rblack42/math-magik-lpp/rst/design_docs/fuselage/fin/index.rst

assembly: fin
#############

..  include::  design_notes.rst

assembly Design File
********************

..  literalinclude::  ../../../../scad/fuselage/fin/fin.scad
    :linenos:
    :caption: fuselage/fin/fin.scad

Component Data File(s)
**********************

..  literalinclude::  ../../../../scad/fuselage/fin/fin_data.scad
    :linenos:
    :caption: fuselage/fin/fin_data.scad

Components
**********

..  toctree::
    :maxdepth: 1

    rib1/index
    rib2/index
    leading_edge/index
    arc/index
    trailing_edge/index
    covering/index

Component Position File
***********************

..  literalinclude::  ../../../../scad/fuselage/fin/fin_pos.scad
    :linenos:
    :caption: fuselage/fin/fin_pos.scad
