rblack42/math-magik-lpp/rst/design_docs/fuselage/motor_stick/index.rst

part: motor_stick
#################

..  include::  design_notes.rst

part Design File
****************

..  literalinclude::  ../../../../scad/fuselage/motor_stick/motor_stick.scad
    :linenos:
    :caption: fuselage/motor_stick/motor_stick.scad

Component Data File(s)
**********************

..  literalinclude::  ../../../../scad/fuselage/motor_stick/motor_stick_data.scad
    :linenos:
    :caption: fuselage/motor_stick/motor_stick_data.scad
