rblack42/math-magik-lpp/rst/design_docs/fuselage/rear_hook/index.rst

part: rear_hook
###############

..  include::  design_notes.rst

part Design File
****************

..  literalinclude::  ../../../../scad/fuselage/rear_hook/rear_hook.scad
    :linenos:
    :caption: fuselage/rear_hook/rear_hook.scad

Component Data File(s)
**********************

..  literalinclude::  ../../../../scad/fuselage/rear_hook/rear_hook_data.scad
    :linenos:
    :caption: fuselage/rear_hook/rear_hook_data.scad
