rblack42/math-magik-lpp/rst/design_docs/fuselage/stab_post/index.rst

part: stab_post
###############

..  include::  design_notes.rst

part Design File
****************

..  literalinclude::  ../../../../scad/fuselage/stab_post/stab_post.scad
    :linenos:
    :caption: fuselage/stab_post/stab_post.scad

Component Data File(s)
**********************

..  literalinclude::  ../../../../scad/fuselage/stab_post/stab_post_data.scad
    :linenos:
    :caption: fuselage/stab_post/stab_post_data.scad
