rblack42/math-magik-lpp/rst/design_docs/fuselage/tail_boom/index.rst

part: tail_boom
###############

..  include::  design_notes.rst

part Design File
****************

..  literalinclude::  ../../../../scad/fuselage/tail_boom/tail_boom.scad
    :linenos:
    :caption: fuselage/tail_boom/tail_boom.scad

Component Data File(s)
**********************

..  literalinclude::  ../../../../scad/fuselage/tail_boom/tail_boom_data.scad
    :linenos:
    :caption: fuselage/tail_boom/tail_boom_data.scad
