rblack42/math-magik-lpp/rst/design_docs/fuselage/thrust_bearing/index.rst

part: thrust_bearing
####################

..  include::  design_notes.rst

part Design File
****************

..  literalinclude::  ../../../../scad/fuselage/thrust_bearing/thrust_bearing.scad
    :linenos:
    :caption: fuselage/thrust_bearing/thrust_bearing.scad

Component Data File(s)
**********************

..  literalinclude::  ../../../../scad/fuselage/thrust_bearing/thrust_bearing_data.scad
    :linenos:
    :caption: fuselage/thrust_bearing/thrust_bearing_data.scad
