rblack42/math-magik-lpp/rst/design_docs/fuselage/wing_post/index.rst

part: wing_post
###############

..  include::  design_notes.rst

part Design File
****************

..  literalinclude::  ../../../../scad/fuselage/wing_post/wing_post.scad
    :linenos:
    :caption: fuselage/wing_post/wing_post.scad

Component Data File(s)
**********************

..  literalinclude::  ../../../../scad/fuselage/wing_post/wing_post_data.scad
    :linenos:
    :caption: fuselage/wing_post/wing_post_data.scad
