rblack42/math-magik-lpp/rst/design_docs/prop/blade/index.rst

part: blade
###########

..  include::  design_notes.rst

part Design File
****************

..  literalinclude::  ../../../../scad/prop/blade/blade.scad
    :linenos:
    :caption: prop/blade/blade.scad
