rblack42/math-magik-lpp/rst/design_docs/prop/spar/index.rst

part: spar
##########

..  include::  design_notes.rst

part Design File
****************

..  literalinclude::  ../../../../scad/prop/spar/spar.scad
    :linenos:
    :caption: prop/spar/spar.scad
