rblack42/math-magik-lpp/rst/design_docs/prop/wire_shaft/index.rst

part: wire_shaft
################

..  include::  design_notes.rst

part Design File
****************

..  literalinclude::  ../../../../scad/prop/wire_shaft/wire_shaft.scad
    :linenos:
    :caption: prop/wire_shaft/wire_shaft.scad
