rblack42/math-magik-lpp/rst/design_docs/stab/left_tip/index.rst

assembly: left_tip
##################

..  include::  design_notes.rst

assembly Design File
********************

..  literalinclude::  ../../../../scad/stab/left_tip/left_tip.scad
    :linenos:
    :caption: stab/left_tip/left_tip.scad

Components
**********

..  toctree::
    :maxdepth: 1

    tip_rib/index
    tip_arc/index
    leading_edge/index
    trailing_edge/index
    covering/index

Component Position File
***********************

..  literalinclude::  ../../../../scad/stab/left_tip/left_tip_pos.scad
    :linenos:
    :caption: stab/left_tip/left_tip_pos.scad
