rblack42/math-magik-lpp/rst/design_docs/wing/center/index.rst

assembly: center
################

..  include::  design_notes.rst

assembly Design File
********************

..  literalinclude::  ../../../../scad/wing/center/center.scad
    :linenos:
    :caption: wing/center/center.scad

Components
**********

..  toctree::
    :maxdepth: 1

    rib/index
    spar/index
    covering/index

Component Position File
***********************

..  literalinclude::  ../../../../scad/wing/center/center_pos.scad
    :linenos:
    :caption: wing/center/center_pos.scad
