rblack42/math-magik-lpp/rst/design_docs/wing/right_tip/index.rst

part: right_tip
###############

..  include::  design_notes.rst

part Design File
****************

..  literalinclude::  ../../../../scad/wing/right_tip/right_tip.scad
    :linenos:
    :caption: wing/right_tip/right_tip.scad
