rblack42/math-magik-lpp/rst/design_docs/wing/Wing_mount/index.rst

part: wing_mount
################

..  include::  design_notes.rst

part Design File
****************

..  literalinclude::  ../../../../scad/wing/Wing_mount/wing_mount.scad
    :linenos:
    :caption: wing/Wing_mount/wing_mount.scad
