rblack42/math-magik-lpp/mmdesigner/fuselage/fin_postrst/design_docs/index.rst

part: 
######

This part is created with the following file:

..  literalinclude::  ../../../scad/fuselage/fin_post/.scad
    :linenos:
    :caption: fuselage/fin_post/.scad
