rblack42/math-magik-lpp/mmdesigner/fuselage/stab_postrst/design_docs/index.rst

part: 
######

This part is created with the following file:

..  literalinclude::  ../../../scad/fuselage/stab_post/.scad
    :linenos:
    :caption: fuselage/stab_post/.scad

Component Data File(s)
**********************

..  literalinclude::  ../scad/fuselage/stab_post/stab_post_data.scad
