rblack42/math-magik-lpp/mmdesigner/fuselage/wing_postrst/design_docs/index.rst

part: 
######

This part is created with the following file:

..  literalinclude::  ../../../scad/fuselage/wing_post/.scad
    :linenos:
    :caption: fuselage/wing_post/.scad

Component Data File(s)
**********************

..  literalinclude::  ../scad/fuselage/wing_post/wing_post_data.scad
