rblack42/math-magik-lpp/mmdesigner/prop/bladerst/design_docs/index.rst

part: blade
###########

This part is created with the following file:

..  literalinclude::  ../../../scad/prop/blade/blade.scad
    :linenos:
    :caption: prop/blade/blade.scad
