rblack42/math-magik-lpp/mmdesigner/prop/sparrst/design_docs/index.rst

part: spar
##########

This part is created with the following file:

..  literalinclude::  ../../../scad/prop/spar/spar.scad
    :linenos:
    :caption: prop/spar/spar.scad
