rblack42/math-magik-lpp/mmdesigner/prop/wire_shaftrst/design_docs/index.rst

part: wire_shaft
################

This part is created with the following file:

..  literalinclude::  ../../../scad/prop/wire_shaft/wire_shaft.scad
    :linenos:
    :caption: prop/wire_shaft/wire_shaft.scad
