rblack42/math-magik-lpp/mmdesigner/wing/right_tiprst/design_docs/index.rst

part: right_tip
###############

This part is created with the following file:

..  literalinclude::  ../../../scad/wing/right_tip/right_tip.scad
    :linenos:
    :caption: wing/right_tip/right_tip.scad
