rblack42/math-magik-lpp/mmdesigner/wing/Wing_mountrst/design_docs/index.rst

part: wing_mount
################

This part is created with the following file:

..  literalinclude::  ../../../scad/wing/Wing_mount/wing_mount.scad
    :linenos:
    :caption: wing/Wing_mount/wing_mount.scad
