rblack42/math-magik-lpp/rst/design_docs/fuselage/fin/arc/index.rst

part: fin_arc
#############

..  include::  design_notes.rst

part Design File
****************

..  literalinclude::  ../../../../../scad/fuselage/fin/arc/fin_arc.scad
    :linenos:
    :caption: fuselage/fin/arc/fin_arc.scad
