rblack42/math-magik-lpp/rst/design_docs/fuselage/fin/covering/index.rst

part: fin_covering
##################

..  include::  design_notes.rst

part Design File
****************

..  literalinclude::  ../../../../../scad/fuselage/fin/covering/fin_covering.scad
    :linenos:
    :caption: fuselage/fin/covering/fin_covering.scad

Component Data File(s)
**********************

..  literalinclude::  ../../../../../scad/fuselage/fin/covering/cover_points.scad
    :linenos:
    :caption: fuselage/fin/covering/cover_points.scad
