rblack42/math-magik-lpp/rst/design_docs/fuselage/fin/leading_edge/index.rst

part: leading_edge
##################

..  include::  design_notes.rst

part Design File
****************

..  literalinclude::  ../../../../../scad/fuselage/fin/leading_edge/leading_edge.scad
    :linenos:
    :caption: fuselage/fin/leading_edge/leading_edge.scad
