rblack42/math-magik-lpp/rst/design_docs/fuselage/fin/rib1/index.rst

part: fin_rib1
##############

..  include::  design_notes.rst

part Design File
****************

..  literalinclude::  ../../../../../scad/fuselage/fin/rib1/fin_rib1.scad
    :linenos:
    :caption: fuselage/fin/rib1/fin_rib1.scad
