rblack42/math-magik-lpp/rst/design_docs/fuselage/fin/rib2/index.rst

part: fin_rib2
##############

..  include::  design_notes.rst

part Design File
****************

..  literalinclude::  ../../../../../scad/fuselage/fin/rib2/fin_rib2.scad
    :linenos:
    :caption: fuselage/fin/rib2/fin_rib2.scad
