rblack42/math-magik-lpp/rst/design_docs/fuselage/fin/trailing_edge/index.rst

part: trailing_edge
###################

..  include::  design_notes.rst

part Design File
****************

..  literalinclude::  ../../../../../scad/fuselage/fin/trailing_edge/trailing_edge.scad
    :linenos:
    :caption: fuselage/fin/trailing_edge/trailing_edge.scad
