rblack42/math-magik-lpp/rst/design_docs/wing/center/covering/index.rst

part: covering
##############

..  include::  design_notes.rst

part Design File
****************

..  literalinclude::  ../../../../../scad/wing/center/covering/covering.scad
    :linenos:
    :caption: wing/center/covering/covering.scad

Component Data File(s)
**********************

..  literalinclude::  ../../../../../scad/wing/center/covering/cover_points.scad
    :linenos:
    :caption: wing/center/covering/cover_points.scad
