rblack42/math-magik-lpp/rst/design_docs/wing/center/rib/index.rst

part: rib
#########

..  include::  design_notes.rst

part Design File
****************

..  literalinclude::  ../../../../../scad/wing/center/rib/rib.scad
    :linenos:
    :caption: wing/center/rib/rib.scad
