rblack42/math-magik-lpp/rst/design_docs/wing/center/spar/index.rst

part: spar
##########

..  include::  design_notes.rst

part Design File
****************

..  literalinclude::  ../../../../../scad/wing/center/spar/spar.scad
    :linenos:
    :caption: wing/center/spar/spar.scad
