rblack42/math-magik-lpp/rst/design_docs/wing/left_tip/covering/index.rst

part: covering
##############

..  include::  design_notes.rst

part Design File
****************

..  literalinclude::  ../../../../../scad/wing/left_tip/covering/covering.scad
    :linenos:
    :caption: wing/left_tip/covering/covering.scad

Component Data File(s)
**********************

..  literalinclude::  ../../../../../scad/wing/left_tip/covering/cover_points.scad
    :linenos:
    :caption: wing/left_tip/covering/cover_points.scad
