rblack42/math-magik-lpp/rst/design_docs/wing/left_tip/leading_edge/index.rst

part: leading_edge
##################

..  include::  design_notes.rst

part Design File
****************

..  literalinclude::  ../../../../../scad/wing/left_tip/leading_edge/leading_edge.scad
    :linenos:
    :caption: wing/left_tip/leading_edge/leading_edge.scad
