rblack42/math-magik-lpp/rst/design_docs/wing/left_tip/tip_arc/index.rst

part: tip_arc
#############

..  include::  design_notes.rst

part Design File
****************

..  literalinclude::  ../../../../../scad/wing/left_tip/tip_arc/tip_arc.scad
    :linenos:
    :caption: wing/left_tip/tip_arc/tip_arc.scad
