rblack42/math-magik-lpp/rst/design_docs/wing/left_tip/tip_rib/index.rst

part: tip_rib
#############

..  include::  design_notes.rst

part Design File
****************

..  literalinclude::  ../../../../../scad/wing/left_tip/tip_rib/tip_rib.scad
    :linenos:
    :caption: wing/left_tip/tip_rib/tip_rib.scad
