rblack42/math-magik-lpp/rst/design_docs/wing/left_tip/trailing_edge/index.rst

part: trailing_edge
###################

..  include::  design_notes.rst

part Design File
****************

..  literalinclude::  ../../../../../scad/wing/left_tip/trailing_edge/trailing_edge.scad
    :linenos:
    :caption: wing/left_tip/trailing_edge/trailing_edge.scad
