rblack42/math-magik-lpp/rst/spelling_wordlist.txt

appveyor
Bigge
bumpversion
cd
cfg
ci
cli
cmd
dev
devnotes
Fairfax
forwardmost
gh
github
gz
Hodson
HTML
init
kbd
Lakehurst
lpp
Macbook
Magik
magik
makefile
Makefile
Makefiles
mmdesigner
nojekyll
numpy
openscad
ornithopter
Pennyplane
py
pypi
rblack
rearmost
readme
repo
rst
slusarczyk
stl
subdirectory
subdirectories
subfolder

Todo
travis
txt
ubuntu
whl
yml
