rblack42/math-magik-lpp/docs/_images/blade.png

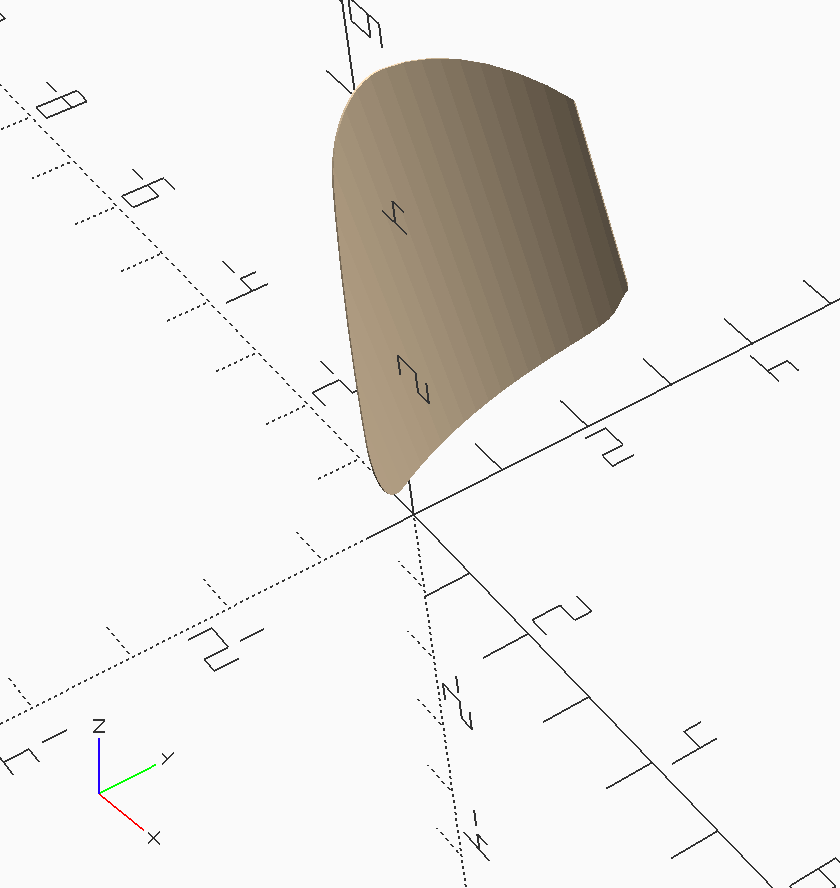
docs/_images/blade.png
