rblack42/math-magik-lpp/docs/_images/double_taper_spar.png

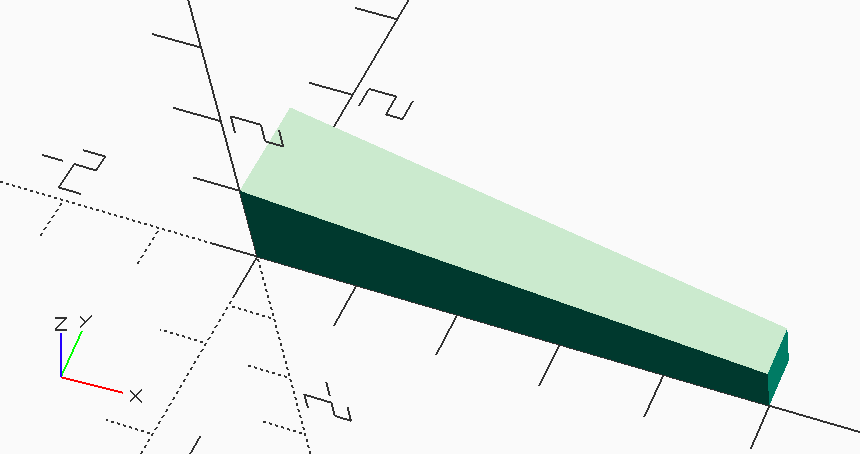
docs/_images/double_taper_spar.png
