rblack42/math-magik-lpp/docs/_images/fuselage.png

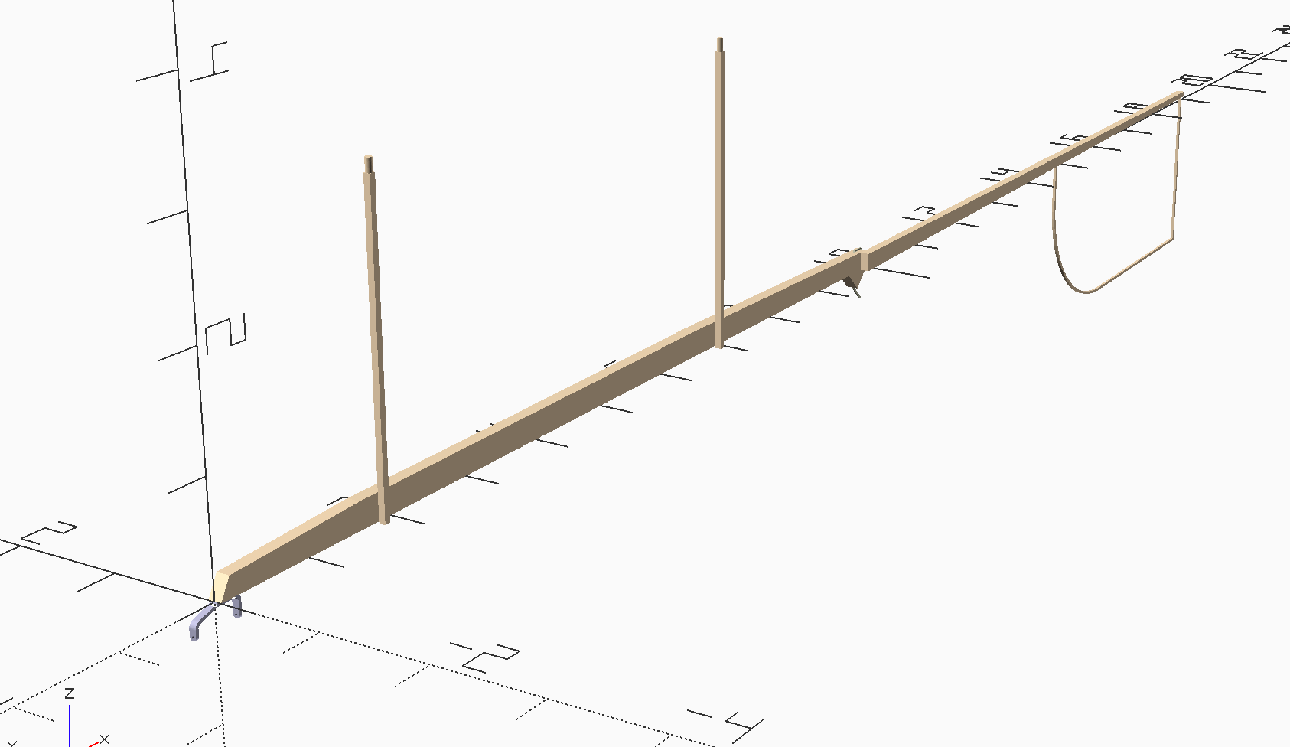
docs/_images/fuselage.png
