rblack42/math-magik-lpp/docs/_images/left_tip.png

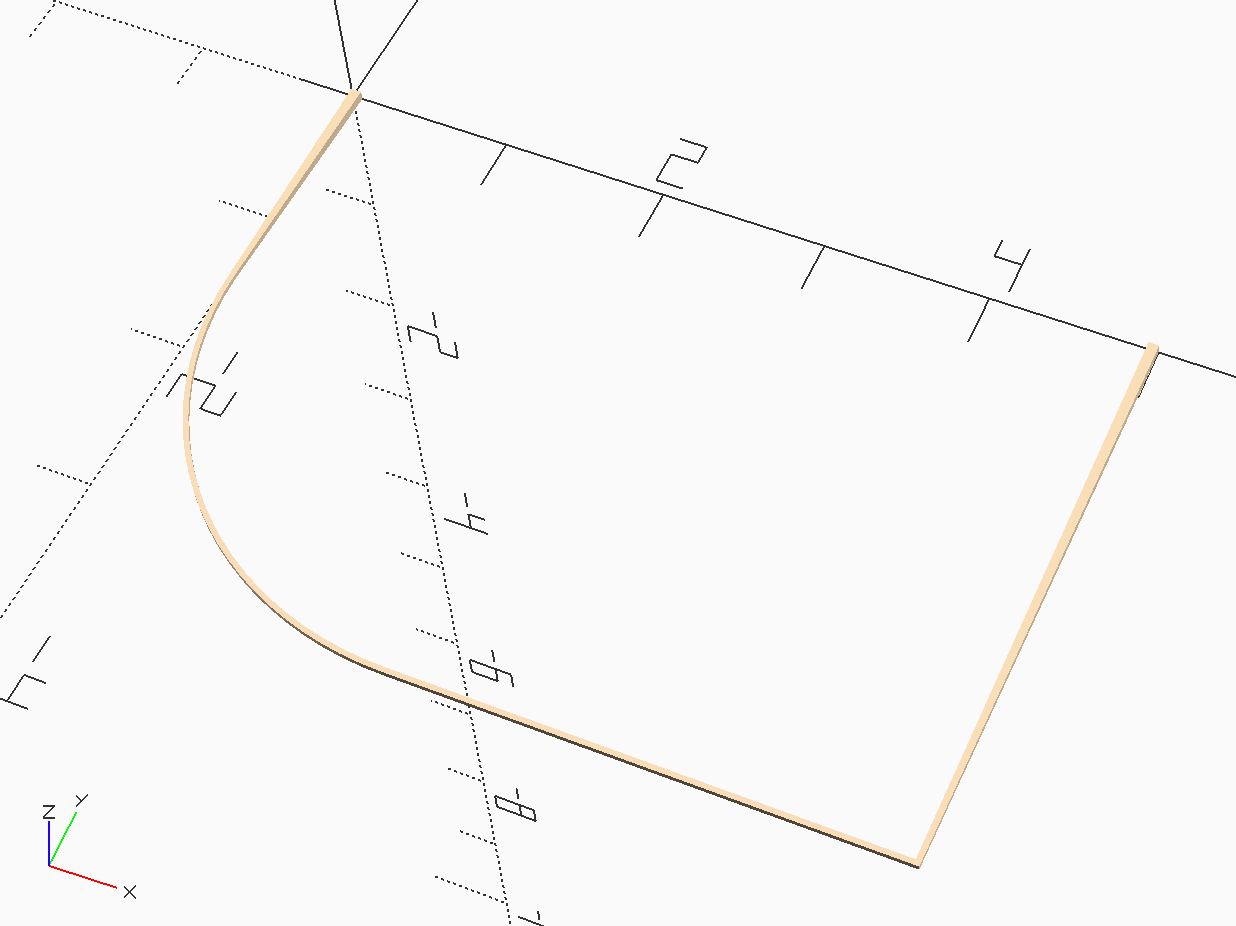
docs/_images/left_tip.png
