rblack42/math-magik-lpp/docs/_images/motor_stick.png

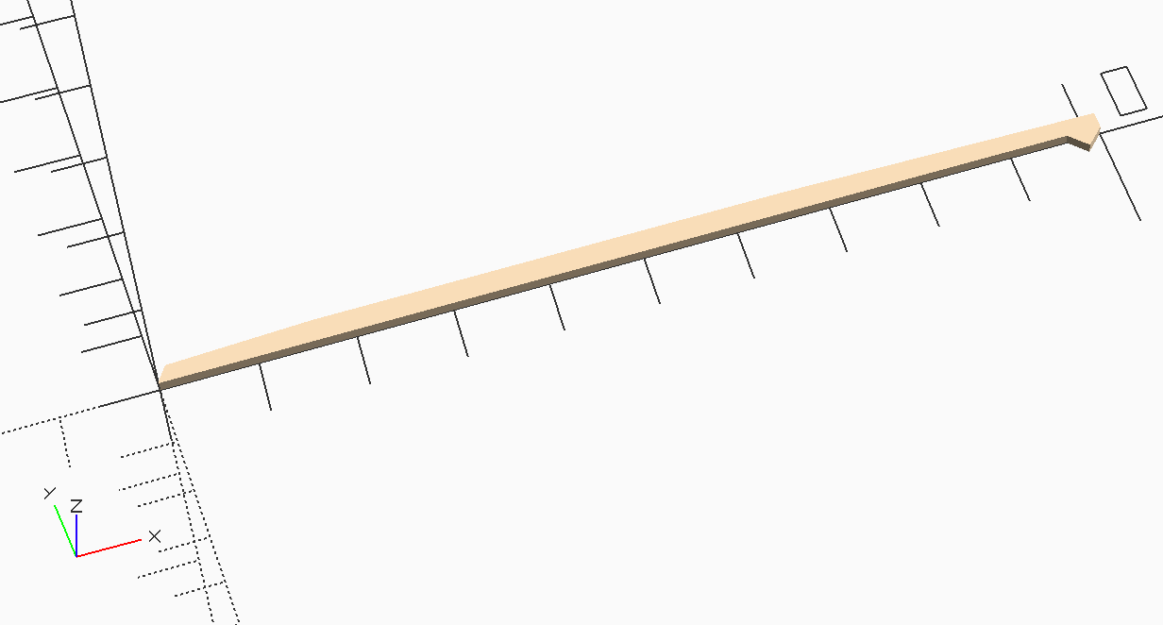
docs/_images/motor_stick.png
