rblack42/math-magik-lpp/docs/_images/prop.png

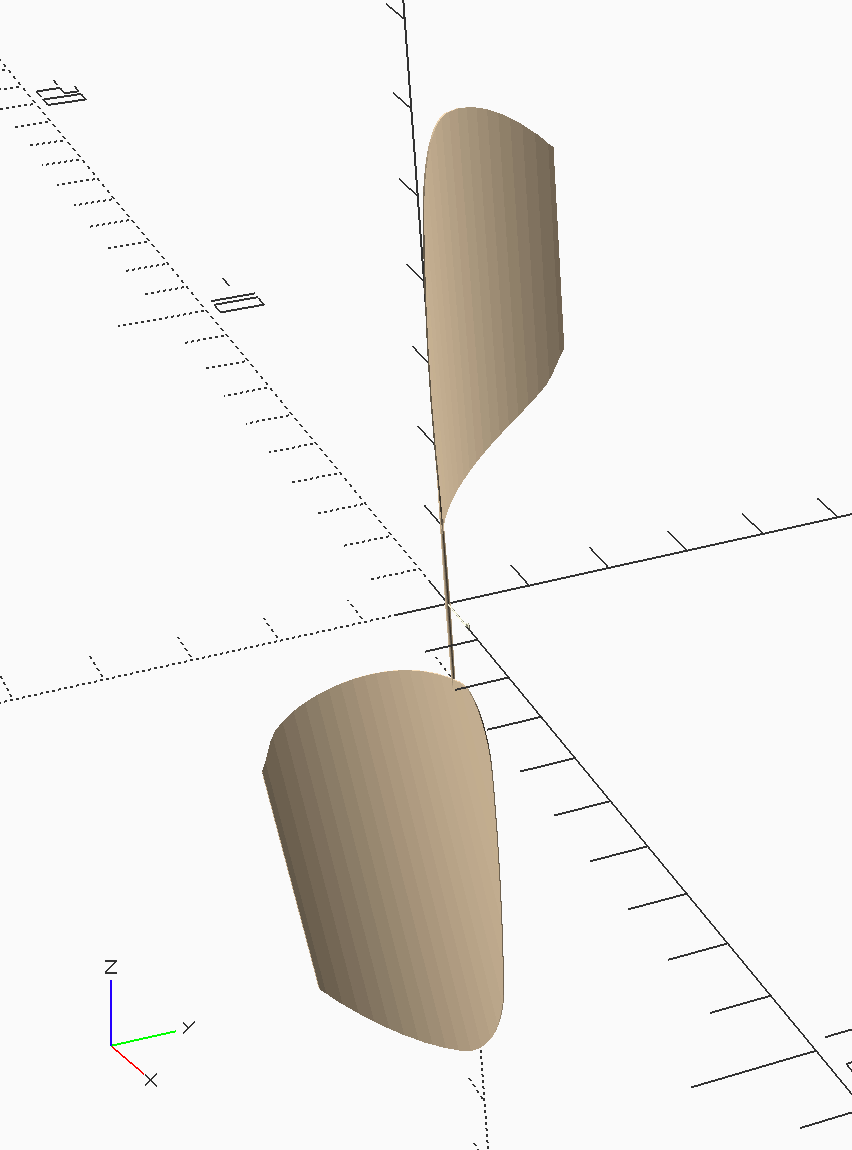
docs/_images/prop.png
