rblack42/math-magik-lpp/docs/_images/rear_hook.png

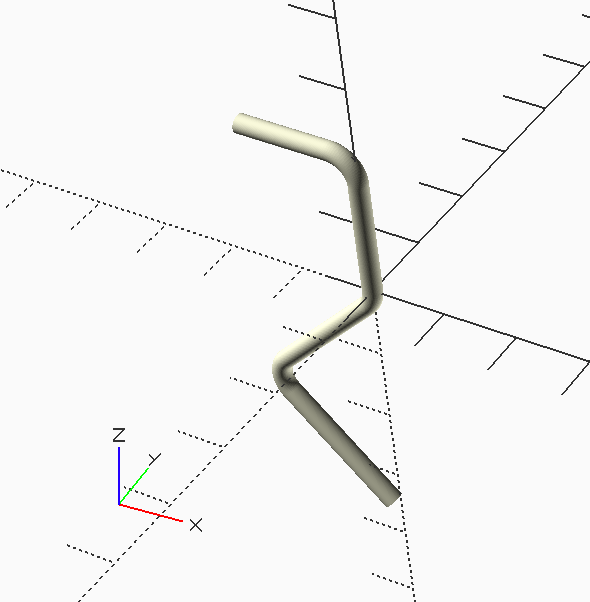
docs/_images/rear_hook.png
