rblack42/math-magik-lpp/docs/_images/rib.png

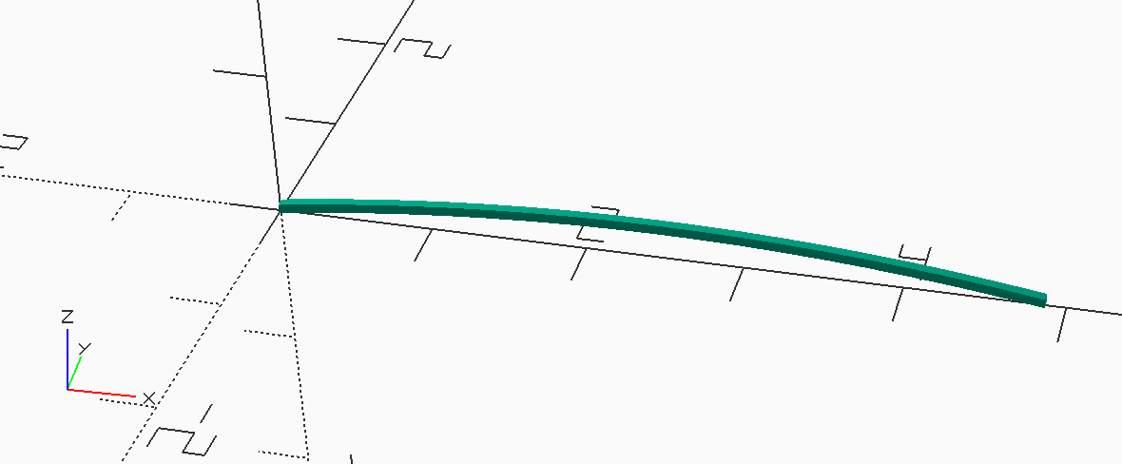
docs/_images/rib.png
