rblack42/math-magik-lpp/docs/_images/rounded_post.png

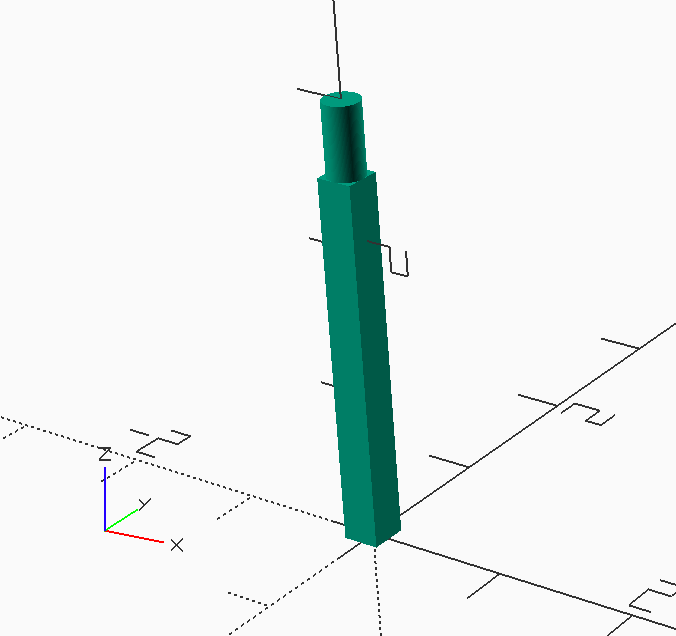
docs/_images/rounded_post.png
