rblack42/math-magik-lpp/docs/_images/single_taper_spar.png

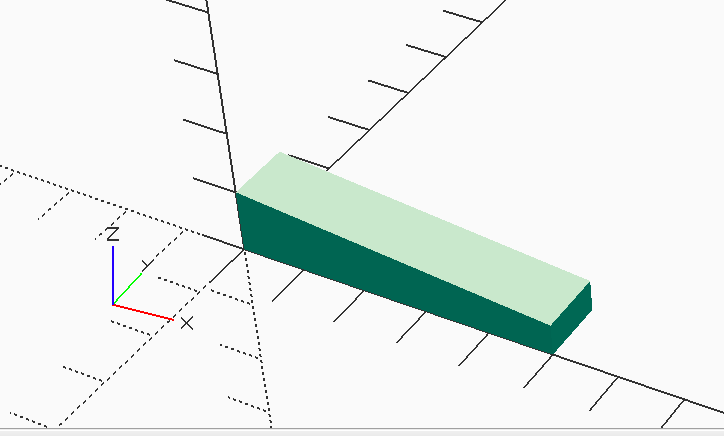
docs/_images/single_taper_spar.png
