rblack42/math-magik-lpp/docs/_images/square_spar.png

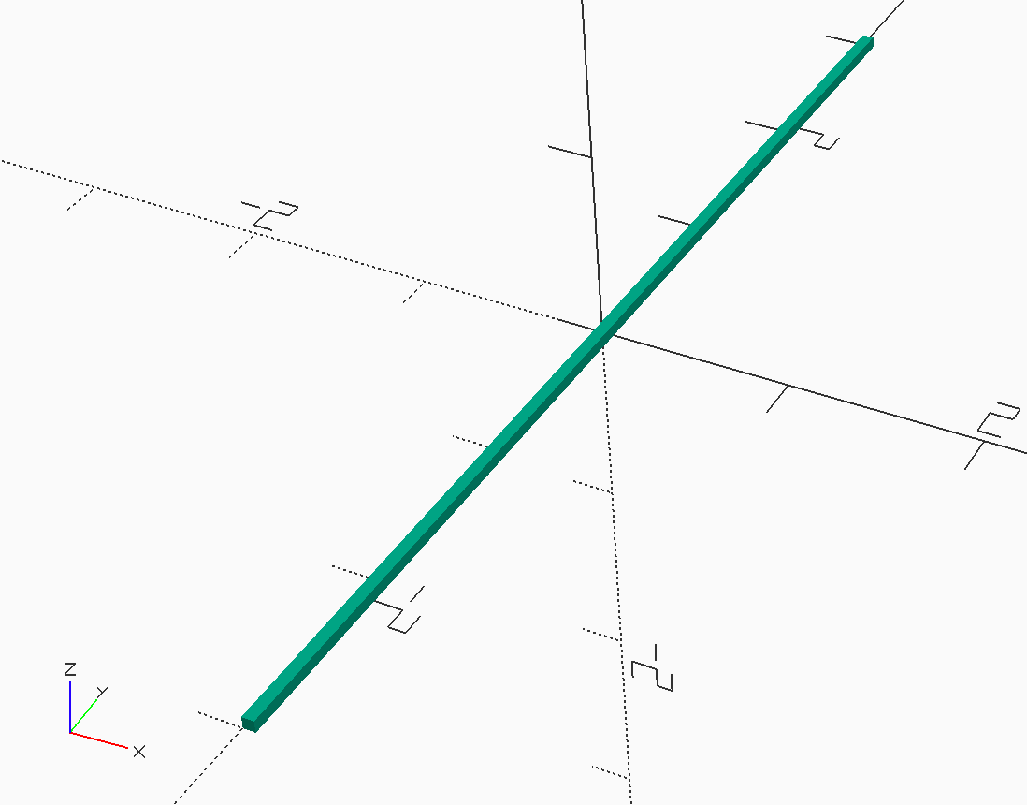
docs/_images/square_spar.png
