rblack42/math-magik-lpp/docs/_images/stab_center.png

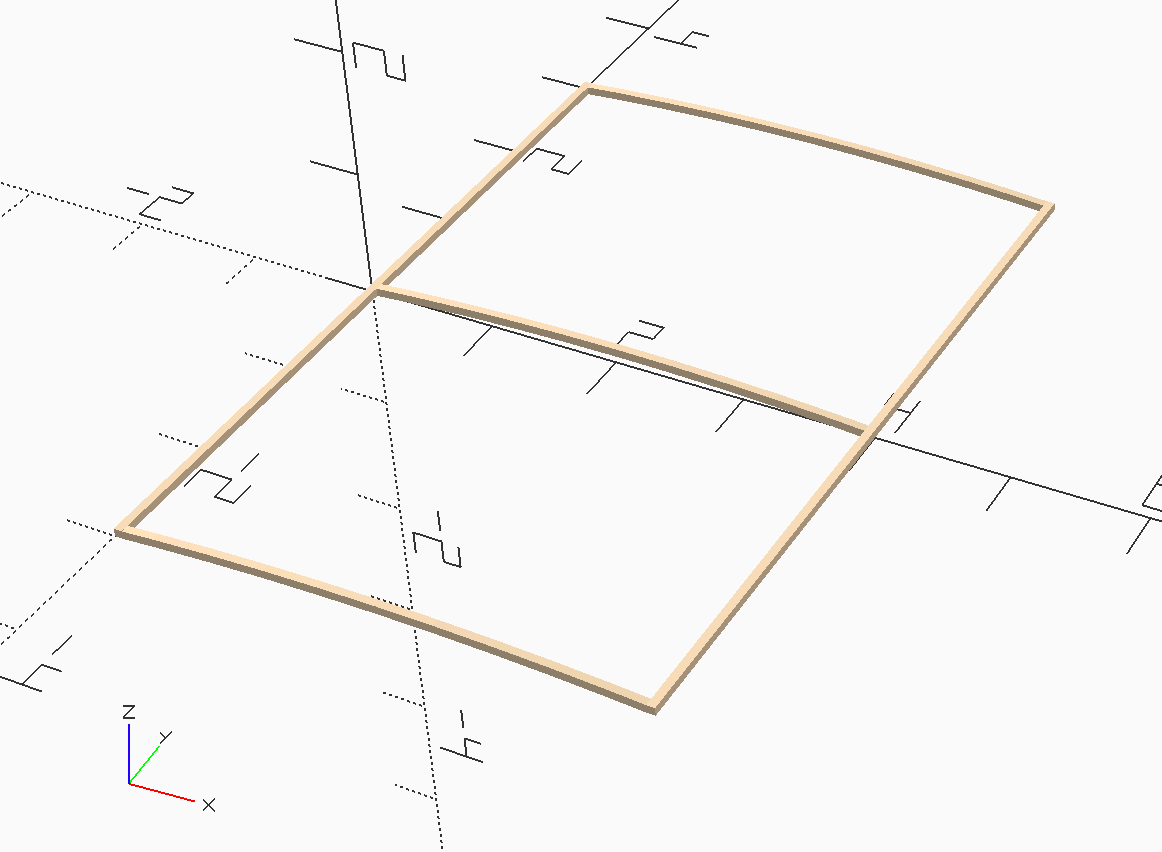
docs/_images/stab_center.png
