rblack42/math-magik-lpp/docs/_images/thrust_bearing.png

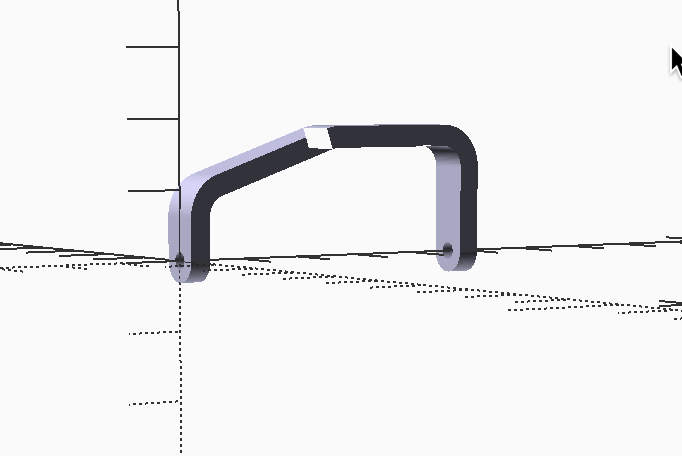
docs/_images/thrust_bearing.png
