rblack42/math-magik-lpp/docs/_images/tikz-1e1b6ad982377da549f57b0fc93ea1e75415a15b.png

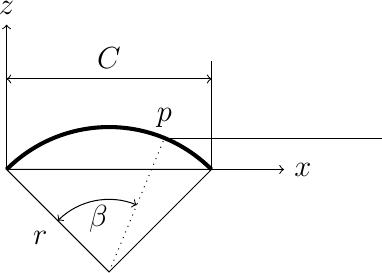
docs/_images/tikz-1e1b6ad982377da549f57b0fc93ea1e75415a15b.png
