rblack42/math-magik-lpp/docs/_images/tikz-3c3cd3720b0a94dc857fa89500e327e3fa3e4184.png

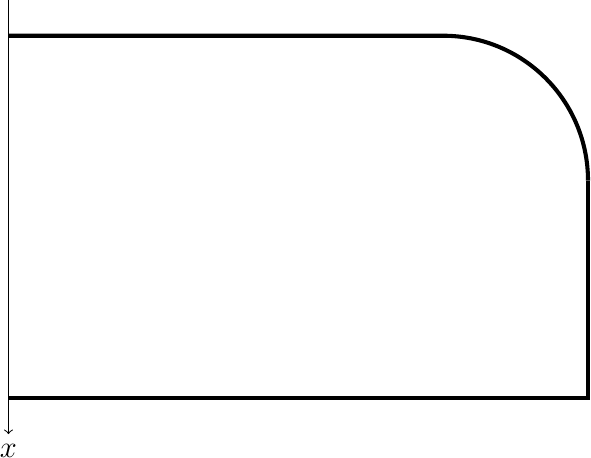
docs/_images/tikz-3c3cd3720b0a94dc857fa89500e327e3fa3e4184.png
