rblack42/math-magik-lpp/docs/_images/tikz-4f54b4c82ac9a10f0b2b195eb7bd98474e7d9e88.png

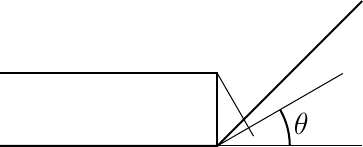
docs/_images/tikz-4f54b4c82ac9a10f0b2b195eb7bd98474e7d9e88.png
