rblack42/math-magik-lpp/docs/_images/tikz-6e44ed49dc1ec410e66353efb7aa8f4e9786132d.png

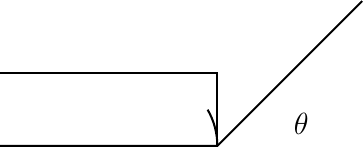
docs/_images/tikz-6e44ed49dc1ec410e66353efb7aa8f4e9786132d.png
