rblack42/math-magik-lpp/docs/_images/tikz-15ca8c3aa0b2c31cfb2b1e34143b804b3e2dcef0.png

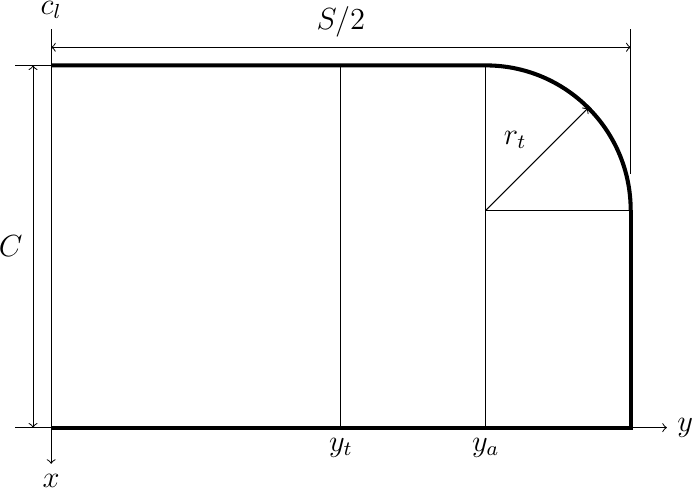
docs/_images/tikz-15ca8c3aa0b2c31cfb2b1e34143b804b3e2dcef0.png
