rblack42/math-magik-lpp/docs/_images/tikz-27d1260bff673aa3068d1d6eca676e5026bad99a.png

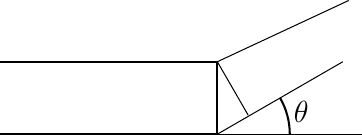
docs/_images/tikz-27d1260bff673aa3068d1d6eca676e5026bad99a.png
