rblack42/math-magik-lpp/docs/_images/tikz-44dbda32ecce6ddc4b5006c9e633f6ff90a8a992.png

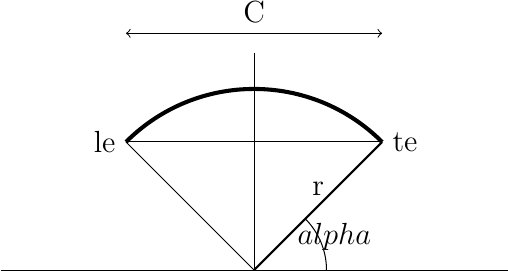
docs/_images/tikz-44dbda32ecce6ddc4b5006c9e633f6ff90a8a992.png
