rblack42/math-magik-lpp/docs/_images/tikz-316b7be6a84d6f8fb4f3c9a147262586597630df.png

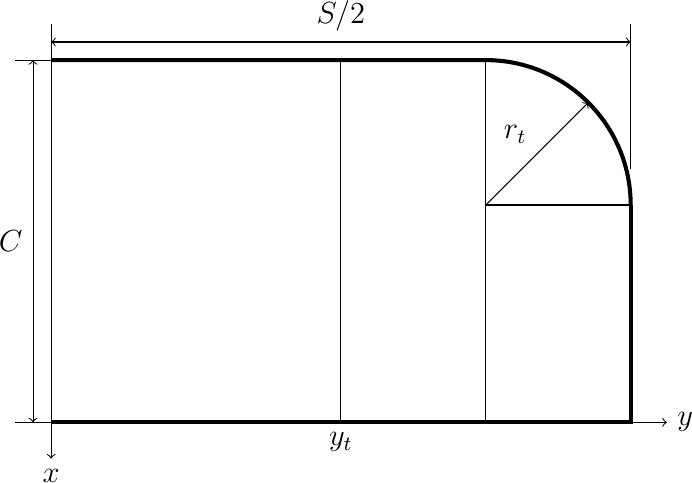
docs/_images/tikz-316b7be6a84d6f8fb4f3c9a147262586597630df.png
