rblack42/math-magik-lpp/docs/_images/tikz-8070c85ff5d8f88f2f3264d625a20d863a9753f6.png

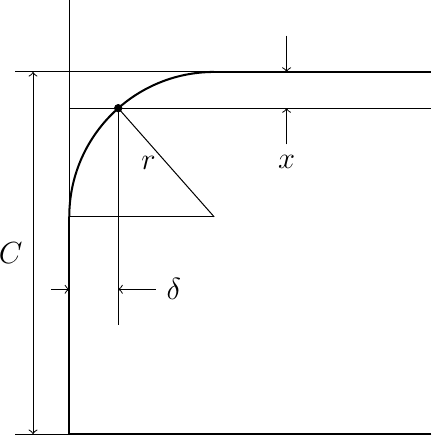
docs/_images/tikz-8070c85ff5d8f88f2f3264d625a20d863a9753f6.png
