rblack42/math-magik-lpp/docs/_images/tikz-32207ebea0998a1cce49b7c706ef4b8a1087978a.png

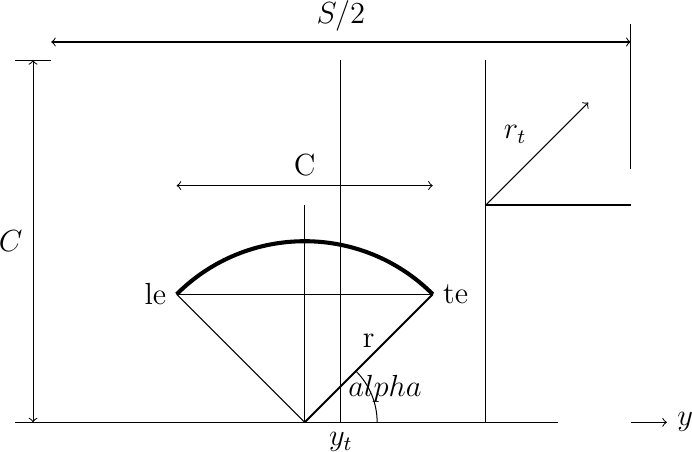
docs/_images/tikz-32207ebea0998a1cce49b7c706ef4b8a1087978a.png
