rblack42/math-magik-lpp/docs/_images/tip_arc.png

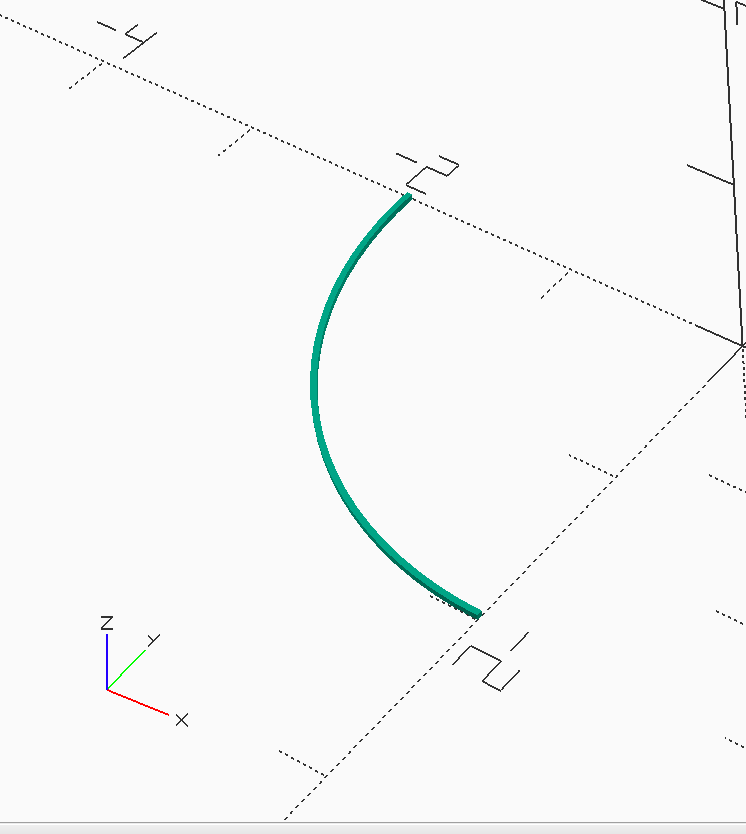
docs/_images/tip_arc.png
