rblack42/math-magik-lpp/docs/_images/wire_shaft.png

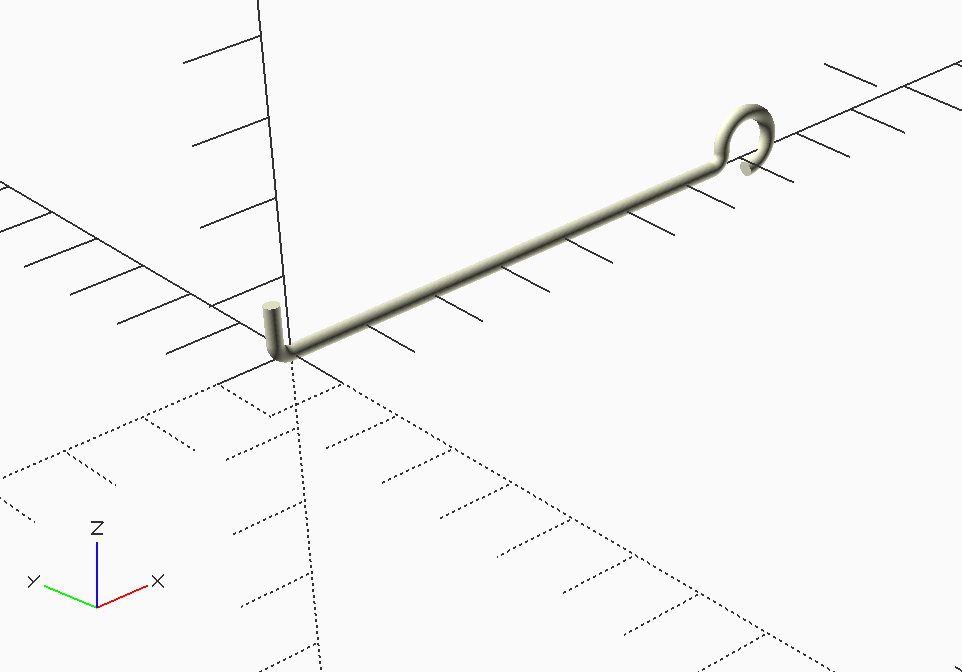
docs/_images/wire_shaft.png
