rblack42/math-magik-lpp/rst/images/mac-terminal.png

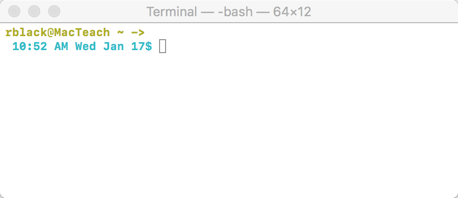
rst/images/mac-terminal.png
