rblack42/math-magik-lpp/scad/math-magik-lpp/prop/spar/spar.stl

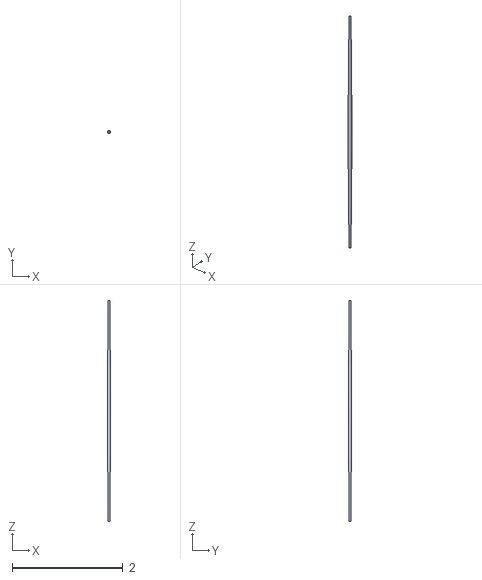
[picture p47: CAD file, 2021-09-04]
scad/math-magik-lpp/prop/spar/spar.stl
0.0625 x 0.0625 x 4.00
