rblack42/math-magik-lpp/scad/math-magik-lpp/rubber_motor/rubber_motor.stl

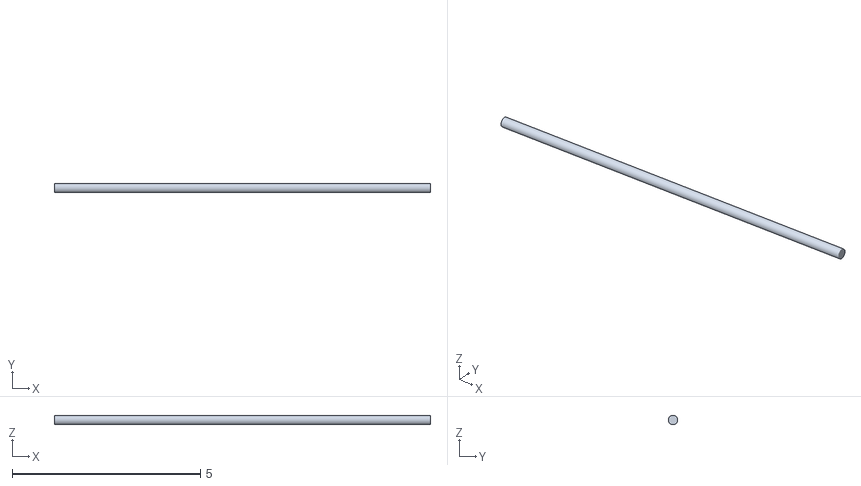
[picture p48: CAD file, 2021-09-04]
scad/math-magik-lpp/rubber_motor/rubber_motor.stl
10.0 x 0.25 x 0.25
