rblack42/math-magik-lpp/scad/math-magik-lpp/stab/center/covering/covering.stl

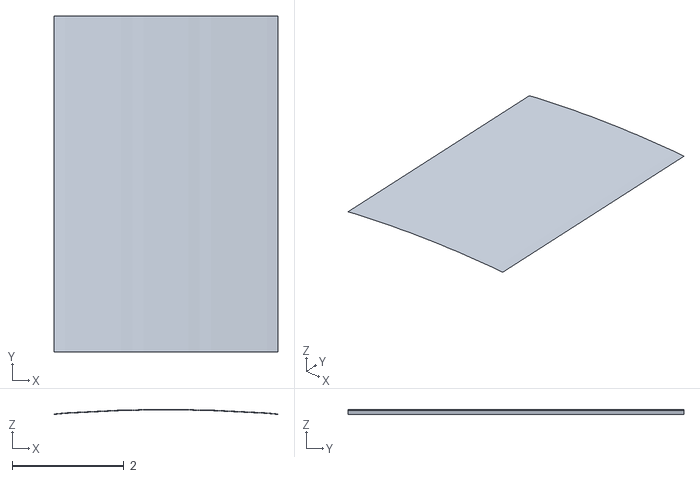
[picture p49: CAD file, 2021-09-04]
scad/math-magik-lpp/stab/center/covering/covering.stl
4.00 x 6.00 x 0.081
