rblack42/math-magik-lpp/scad/math-magik-lpp/stab/center/rib/rib.stl

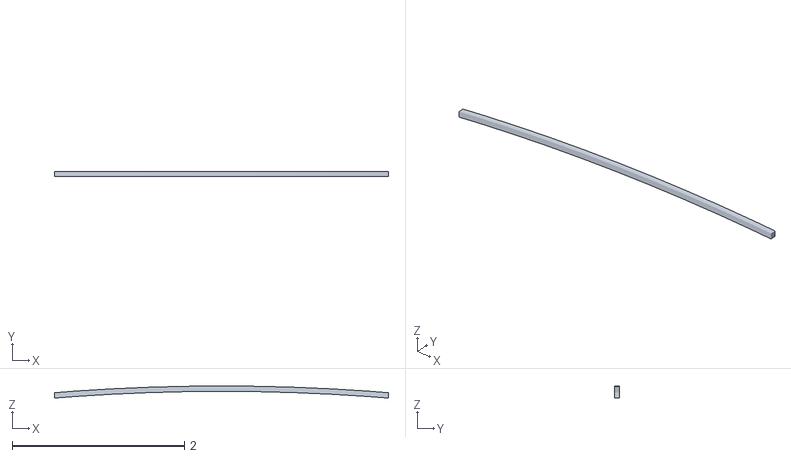
[picture p50: CAD file, 2021-09-04]
scad/math-magik-lpp/stab/center/rib/rib.stl
3.88 x 0.0625 x 0.14
