rblack42/math-magik-lpp/scad/math-magik-lpp/stab/center/spar/spar.stl

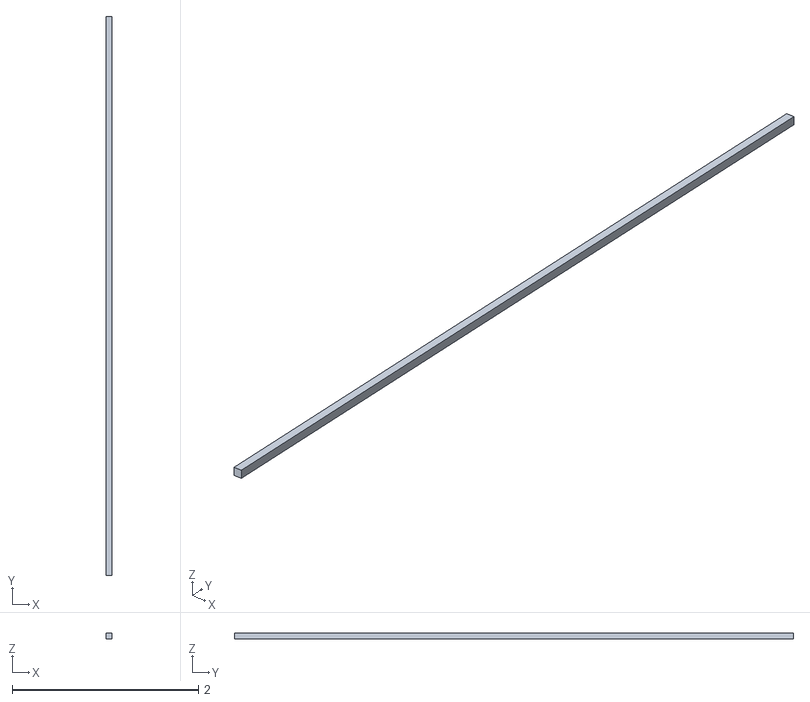
[picture p51: CAD file, 2021-09-04]
scad/math-magik-lpp/stab/center/spar/spar.stl
0.0625 x 6.00 x 0.0625
