rblack42/math-magik-lpp/scad/math-magik-lpp/stab/left_tip/covering/covering.stl

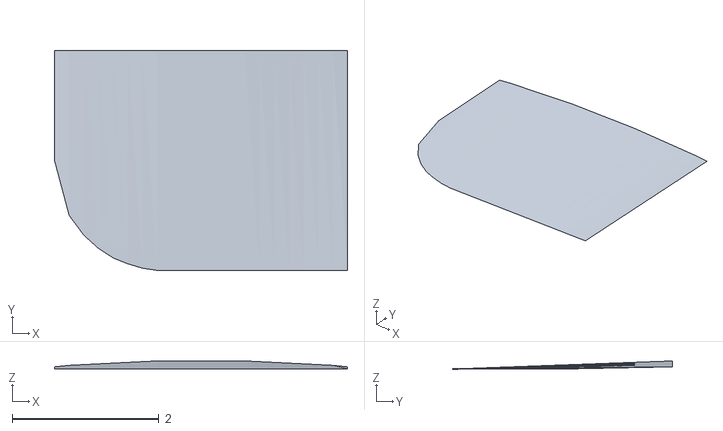
[picture p52: CAD file, 2021-09-04]
scad/math-magik-lpp/stab/left_tip/covering/covering.stl
4.00 x 3.00 x 0.111
