rblack42/math-magik-lpp/scad/math-magik-lpp/stab/left_tip/leading_edge/leading_edge.stl

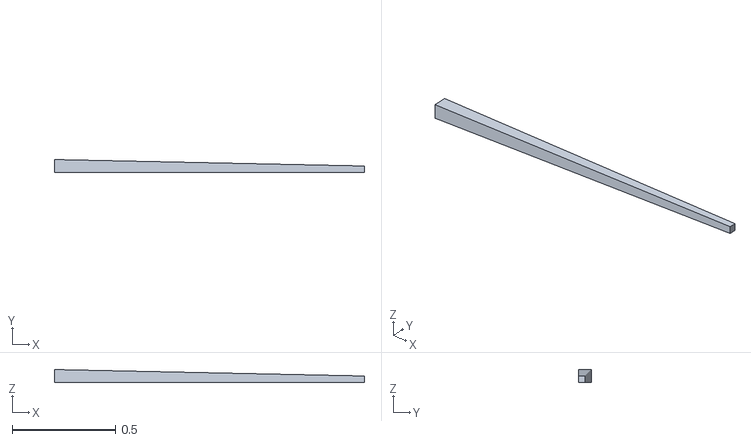
[picture p53: CAD file, 2021-09-04]
scad/math-magik-lpp/stab/left_tip/leading_edge/leading_edge.stl
1.50 x 0.0625 x 0.0625
