rblack42/math-magik-lpp/scad/math-magik-lpp/stab/left_tip/tip_rib/tip_rib.stl

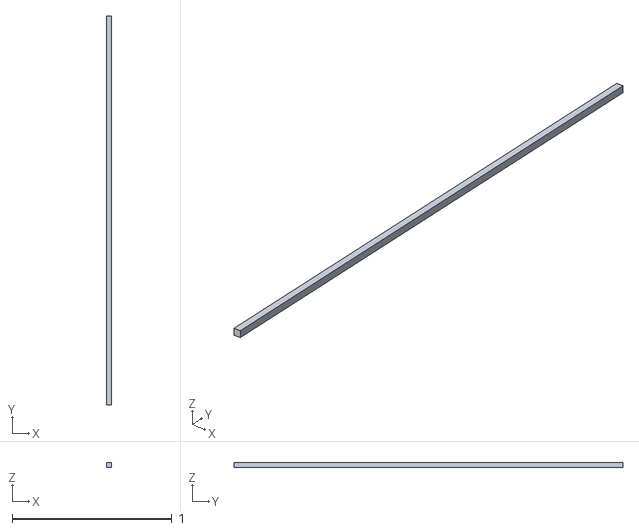
[picture p54: CAD file, 2021-09-04]
scad/math-magik-lpp/stab/left_tip/tip_rib/tip_rib.stl
0.0312 x 2.44 x 0.0312
