rblack42/math-magik-lpp/scad/math-magik-lpp/stab/left_tip/trailing_edge/trailing_edge.stl

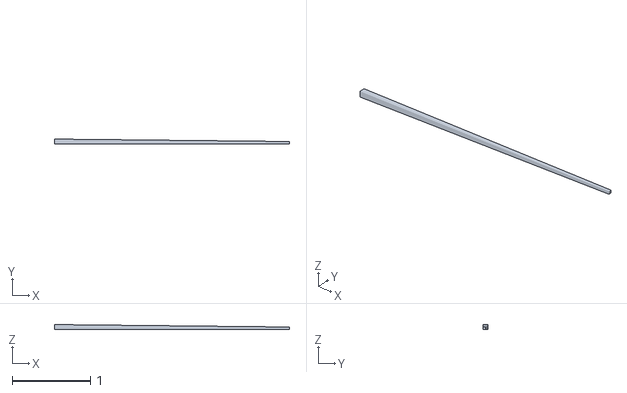
[picture p55: CAD file, 2021-09-04]
scad/math-magik-lpp/stab/left_tip/trailing_edge/trailing_edge.stl
3.00 x 0.0625 x 0.0625
