rblack42/math-magik-lpp/scad/math-magik-lpp/stab/right_tip/right_tip.stl

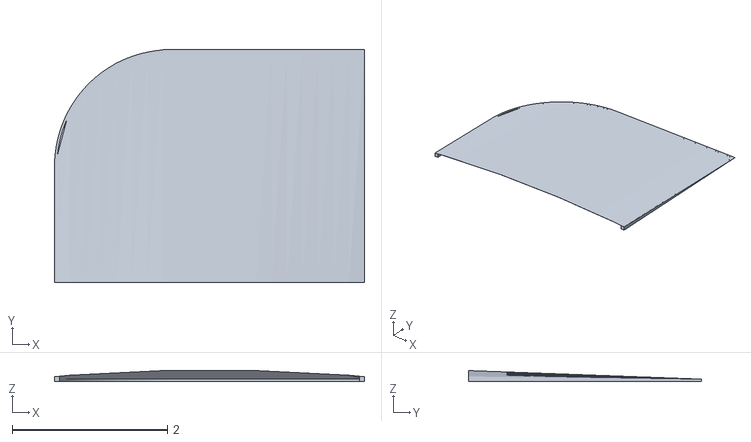
[picture p56: CAD file, 2021-09-04]
scad/math-magik-lpp/stab/right_tip/right_tip.stl
4.00 x 3.00 x 0.14
