rblack42/math-magik-lpp/scad/math-magik-lpp/stab/stab_mount/stab_mount.stl

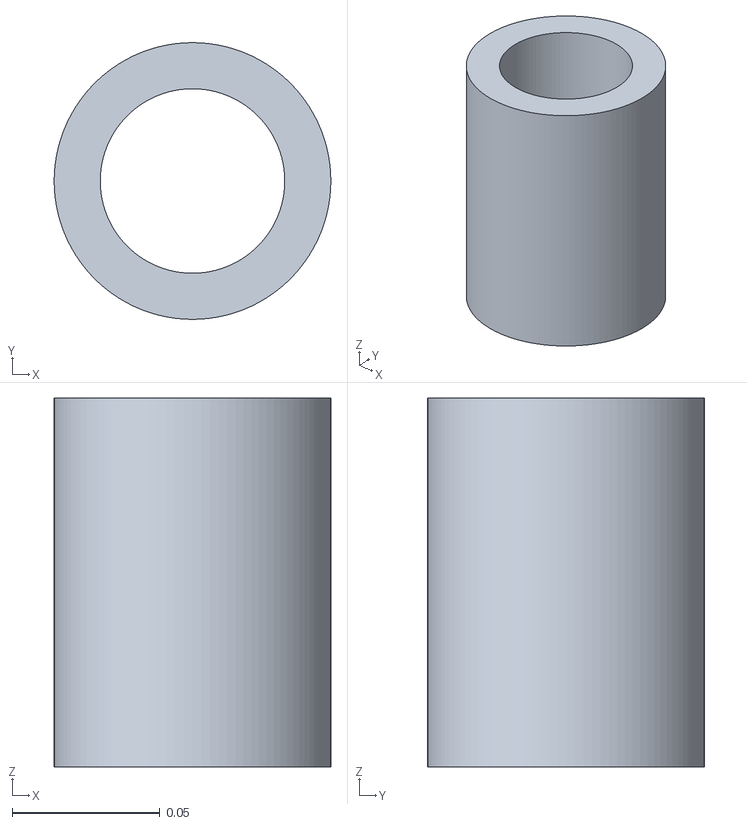
[picture p57: CAD file, 2021-09-04]
scad/math-magik-lpp/stab/stab_mount/stab_mount.stl
0.0938 x 0.0938 x 0.125
