rblack42/math-magik-lpp/scad/math-magik-lpp/wing/center/covering/covering.stl

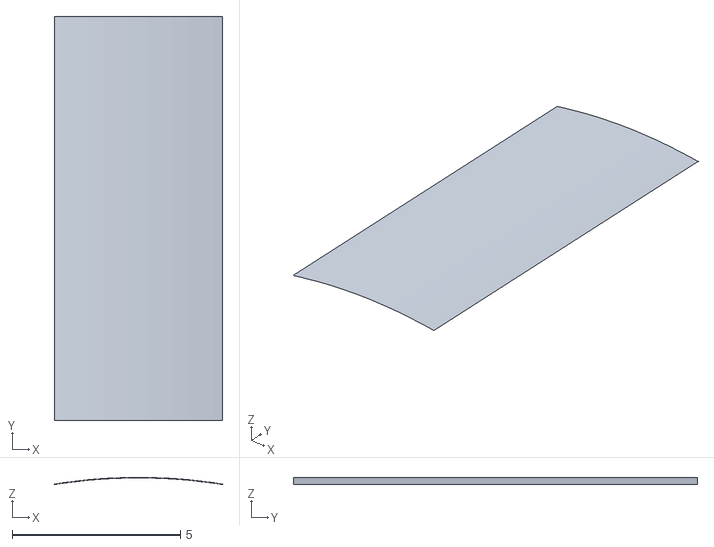
[picture p58: CAD file, 2021-09-04]
scad/math-magik-lpp/wing/center/covering/covering.stl
5.00 x 12.0 x 0.201
