rblack42/math-magik-lpp/scad/math-magik-lpp/wing/center/rib/rib.stl

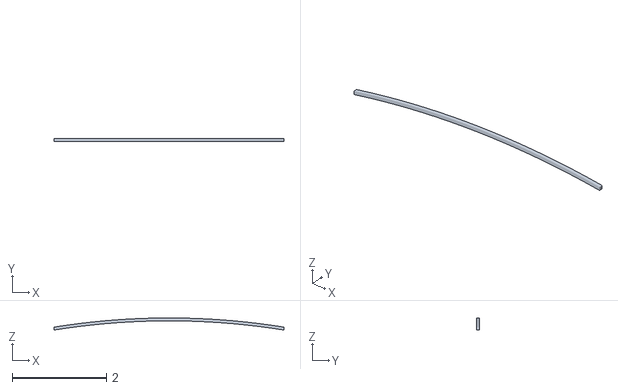
[picture p59: CAD file, 2021-09-04]
scad/math-magik-lpp/wing/center/rib/rib.stl
4.88 x 0.0625 x 0.257
