rblack42/math-magik-lpp/scad/math-magik-lpp/wing/center/spar/spar.stl

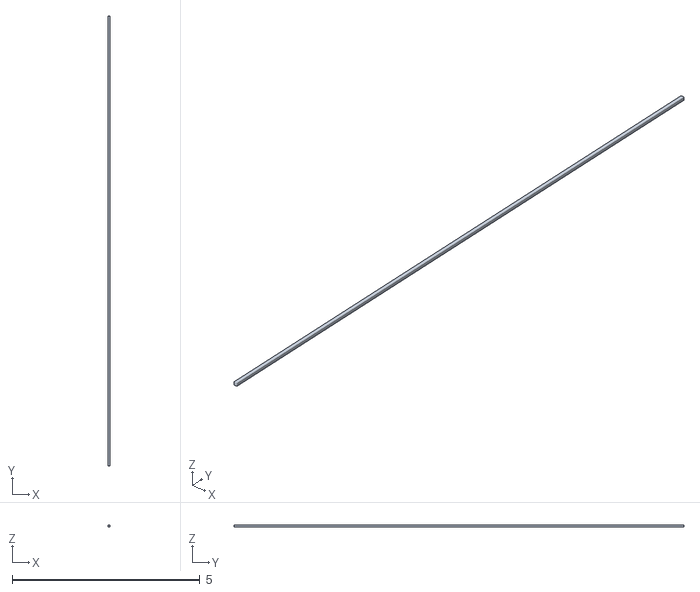
[picture p60: CAD file, 2021-09-04]
scad/math-magik-lpp/wing/center/spar/spar.stl
0.0625 x 12.0 x 0.0625
