rblack42/math-magik-lpp/scad/math-magik-lpp/wing/left_tip/covering/covering.stl

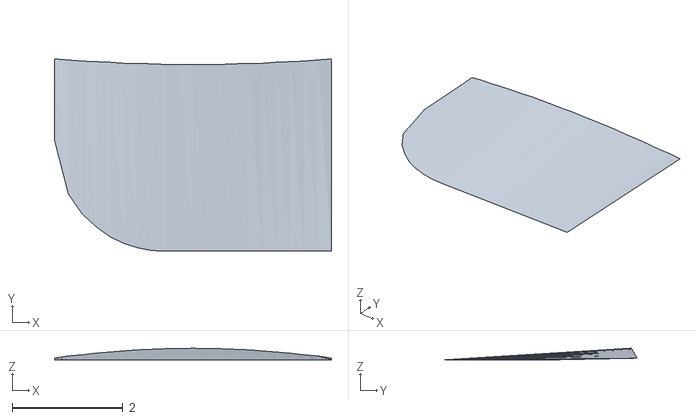
[picture p61: CAD file, 2021-09-04]
scad/math-magik-lpp/wing/left_tip/covering/covering.stl
5.00 x 3.47 x 0.211
