rblack42/math-magik-lpp/scad/math-magik-lpp/wing/left_tip/leading_edge/leading_edge.stl

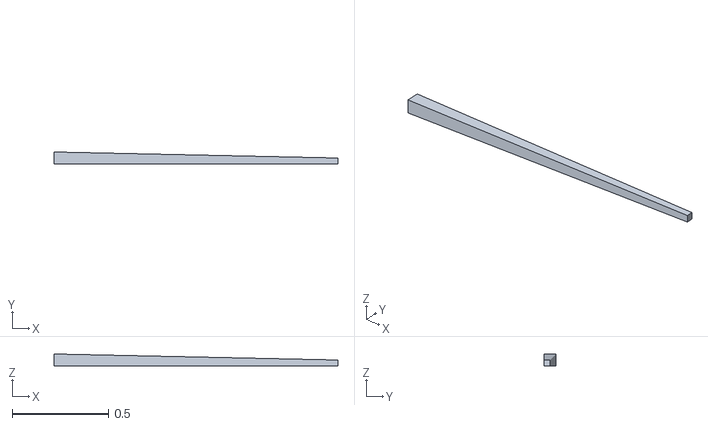
[picture p62: CAD file, 2021-09-04]
scad/math-magik-lpp/wing/left_tip/leading_edge/leading_edge.stl
1.47 x 0.0625 x 0.0625
