rblack42/math-magik-lpp/scad/math-magik-lpp/wing/left_tip/tip_arc/tip_arc.stl

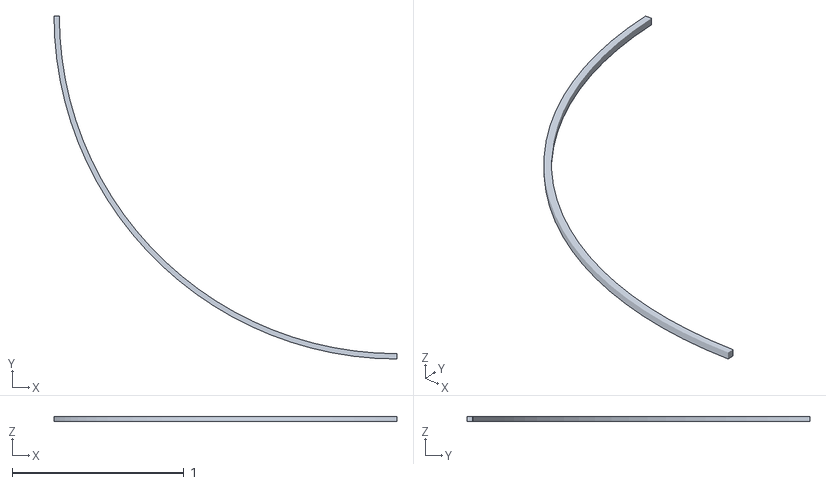
[picture p63: CAD file, 2021-09-04]
scad/math-magik-lpp/wing/left_tip/tip_arc/tip_arc.stl
2.00 x 2.00 x 0.0312
