rblack42/math-magik-lpp/scad/math-magik-lpp/wing/right_tip/right_tip.stl

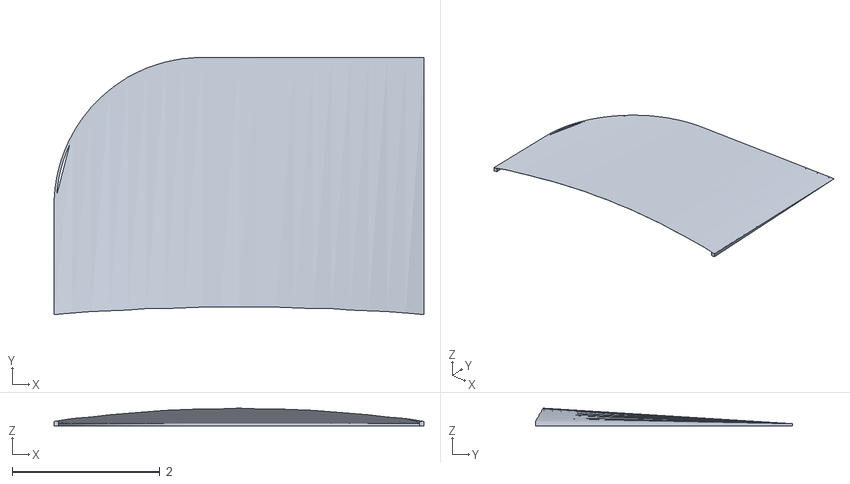
[picture p66: CAD file, 2021-09-04]
scad/math-magik-lpp/wing/right_tip/right_tip.stl
5.00 x 3.47 x 0.24
