rblack42/math-magik-lpp/scad/math-magik-lpp/rubber_motor/rubber_motor_data.scad

//###################################################
// rubber_motor_data.scad - Math-Magik-LPP
// (c) 2021 by Roie R Black
//===================================================

density = 10.8864;

rubber_motor_length = 10;
rubber_motor_radius = 1/8;
