rblack42/math-magik-lpp/mmdesigner/fin_tip_cover_points.scad

g_pts = [
    [
        [0.00, 0.00, 0.00],[0.20, 0.00, 0.00],[0.40, 0.00, 0.00],[0.60, 0.00, 0.00],[0.80, 0.00, 0.00],[1.00, 0.00, 0.00],[1.20, 0.00, 0.00],[1.40, 0.00, 0.00],[1.60, 0.00, 0.00],[1.80, 0.00, 0.00],[2.00, 0.00, 0.00],[2.20, 0.00, 0.00],[2.40, 0.00, 0.00],[2.60, 0.00, 0.00],[2.80, 0.00, 0.00],[3.00, 0.00, 0.00],[3.20, 0.00, 0.00],[3.40, 0.00, 0.00],[3.60, 0.00, 0.00],[3.80, 0.00, 0.00],[4.00, 0.00, 0.00]
    ],
    [
        [0.00, 0.10, 0.00],[0.20, 0.10, 0.00],[0.40, 0.10, 0.00],[0.60, 0.10, 0.00],[0.80, 0.10, 0.00],[1.00, 0.10, 0.00],[1.20, 0.10, 0.00],[1.40, 0.10, 0.00],[1.60, 0.10, 0.00],[1.80, 0.10, 0.00],[2.00, 0.10, 0.00],[2.20, 0.10, 0.00],[2.40, 0.10, 0.00],[2.60, 0.10, 0.00],[2.80, 0.10, 0.00],[3.00, 0.10, 0.00],[3.20, 0.10, 0.00],[3.40, 0.10, 0.00],[3.60, 0.10, 0.00],[3.80, 0.10, 0.00],[4.00, 0.10, 0.00]
    ],
    [
        [0.00, 0.20, 0.00],[0.20, 0.20, 0.00],[0.40, 0.20, 0.00],[0.60, 0.20, 0.00],[0.80, 0.20, 0.00],[1.00, 0.20, 0.00],[1.20, 0.20, 0.00],[1.40, 0.20, 0.00],[1.60, 0.20, 0.00],[1.80, 0.20, 0.00],[2.00, 0.20, 0.00],[2.20, 0.20, 0.00],[2.40, 0.20, 0.00],[2.60, 0.20, 0.00],[2.80, 0.20, 0.00],[3.00, 0.20, 0.00],[3.20, 0.20, 0.00],[3.40, 0.20, 0.00],[3.60, 0.20, 0.00],[3.80, 0.20, 0.00],[4.00, 0.20, 0.00]
    ],
    [
        [0.00, 0.30, 0.00],[0.20, 0.30, 0.00],[0.40, 0.30, 0.00],[0.60, 0.30, 0.00],[0.80, 0.30, 0.00],[1.00, 0.30, 0.00],[1.20, 0.30, 0.00],[1.40, 0.30, 0.00],[1.60, 0.30, 0.00],[1.80, 0.30, 0.00],[2.00, 0.30, 0.00],[2.20, 0.30, 0.00],[2.40, 0.30, 0.00],[2.60, 0.30, 0.00],[2.80, 0.30, 0.00],[3.00, 0.30, 0.00],[3.20, 0.30, 0.00],[3.40, 0.30, 0.00],[3.60, 0.30, 0.00],[3.80, 0.30, 0.00],[4.00, 0.30, 0.00]
    ],
    [
        [0.00, 0.40, 0.00],[0.20, 0.40, 0.00],[0.40, 0.40, 0.00],[0.60, 0.40, 0.00],[0.80, 0.40, 0.00],[1.00, 0.40, 0.00],[1.20, 0.40, 0.00],[1.40, 0.40, 0.00],[1.60, 0.40, 0.00],[1.80, 0.40, 0.00],[2.00, 0.40, 0.00],[2.20, 0.40, 0.00],[2.40, 0.40, 0.00],[2.60, 0.40, 0.00],[2.80, 0.40, 0.00],[3.00, 0.40, 0.00],[3.20, 0.40, 0.00],[3.40, 0.40, 0.00],[3.60, 0.40, 0.00],[3.80, 0.40, 0.00],[4.00, 0.40, 0.00]
    ],
    [
        [0.00, 0.50, 0.00],[0.20, 0.50, 0.00],[0.40, 0.50, 0.00],[0.60, 0.50, 0.00],[0.80, 0.50, 0.00],[1.00, 0.50, 0.00],[1.20, 0.50, 0.00],[1.40, 0.50, 0.00],[1.60, 0.50, 0.00],[1.80, 0.50, 0.00],[2.00, 0.50, 0.00],[2.20, 0.50, 0.00],[2.40, 0.50, 0.00],[2.60, 0.50, 0.00],[2.80, 0.50, 0.00],[3.00, 0.50, 0.00],[3.20, 0.50, 0.00],[3.40, 0.50, 0.00],[3.60, 0.50, 0.00],[3.80, 0.50, 0.00],[4.00, 0.50, 0.00]
    ],
    [
        [0.00, 0.60, 0.00],[0.20, 0.60, 0.00],[0.40, 0.60, 0.00],[0.60, 0.60, 0.00],[0.80, 0.60, 0.00],[1.00, 0.60, 0.00],[1.20, 0.60, 0.00],[1.40, 0.60, 0.00],[1.60, 0.60, 0.00],[1.80, 0.60, 0.00],[2.00, 0.60, 0.00],[2.20, 0.60, 0.00],[2.40, 0.60, 0.00],[2.60, 0.60, 0.00],[2.80, 0.60, 0.00],[3.00, 0.60, 0.00],[3.20, 0.60, 0.00],[3.40, 0.60, 0.00],[3.60, 0.60, 0.00],[3.80, 0.60, 0.00],[4.00, 0.60, 0.00]
    ],
    [
        [0.00, 0.70, 0.00],[0.20, 0.70, 0.00],[0.40, 0.70, 0.00],[0.60, 0.70, 0.00],[0.80, 0.70, 0.00],[1.00, 0.70, 0.00],[1.20, 0.70, 0.00],[1.40, 0.70, 0.00],[1.59, 0.70, 0.00],[1.79, 0.70, 0.00],[1.99, 0.70, 0.00],[2.19, 0.70, 0.00],[2.39, 0.70, 0.00],[2.59, 0.70, 0.00],[2.79, 0.70, 0.00],[2.99, 0.70, 0.00],[3.19, 0.70, 0.00],[3.39, 0.70, 0.00],[3.59, 0.70, 0.00],[3.79, 0.70, 0.00],[3.99, 0.70, 0.00]
    ],
    [
        [0.00, 0.80, 0.00],[0.20, 0.80, 0.00],[0.40, 0.80, 0.00],[0.60, 0.80, 0.00],[0.79, 0.80, 0.00],[0.99, 0.80, 0.00],[1.19, 0.80, 0.00],[1.39, 0.80, 0.00],[1.59, 0.80, 0.00],[1.79, 0.80, 0.00],[1.98, 0.80, 0.00],[2.18, 0.80, 0.00],[2.38, 0.80, 0.00],[2.58, 0.80, 0.00],[2.78, 0.80, 0.00],[2.98, 0.80, 0.00],[3.18, 0.80, 0.00],[3.37, 0.80, 0.00],[3.57, 0.80, 0.00],[3.77, 0.80, 0.00],[3.97, 0.80, 0.00]
    ],
    [
        [0.00, 0.90, 0.00],[0.20, 0.90, 0.00],[0.39, 0.90, 0.00],[0.59, 0.90, 0.00],[0.79, 0.90, 0.00],[0.99, 0.90, 0.00],[1.18, 0.90, 0.00],[1.38, 0.90, 0.00],[1.58, 0.90, 0.00],[1.78, 0.90, 0.00],[1.97, 0.90, 0.00],[2.17, 0.90, 0.00],[2.37, 0.90, 0.00],[2.56, 0.90, 0.00],[2.76, 0.90, 0.00],[2.96, 0.90, 0.00],[3.16, 0.90, 0.00],[3.35, 0.90, 0.00],[3.55, 0.90, 0.00],[3.75, 0.90, 0.00],[3.95, 0.90, 0.00]
    ],
    [
        [0.00, 1.00, 0.00],[0.20, 1.00, 0.00],[0.39, 1.00, 0.00],[0.59, 1.00, 0.00],[0.78, 1.00, 0.00],[0.98, 1.00, 0.00],[1.17, 1.00, 0.00],[1.37, 1.00, 0.00],[1.57, 1.00, 0.00],[1.76, 1.00, 0.00],[1.96, 1.00, 0.00],[2.15, 1.00, 0.00],[2.35, 1.00, 0.00],[2.54, 1.00, 0.00],[2.74, 1.00, 0.00],[2.94, 1.00, 0.00],[3.13, 1.00, 0.00],[3.33, 1.00, 0.00],[3.52, 1.00, 0.00],[3.72, 1.00, 0.00],[3.91, 1.00, 0.00]
    ],
    [
        [0.00, 1.10, 0.00],[0.19, 1.10, 0.00],[0.39, 1.10, 0.00],[0.58, 1.10, 0.00],[0.77, 1.10, 0.00],[0.97, 1.10, 0.00],[1.16, 1.10, 0.00],[1.36, 1.10, 0.00],[1.55, 1.10, 0.00],[1.74, 1.10, 0.00],[1.94, 1.10, 0.00],[2.13, 1.10, 0.00],[2.32, 1.10, 0.00],[2.52, 1.10, 0.00],[2.71, 1.10, 0.00],[2.91, 1.10, 0.00],[3.10, 1.10, 0.00],[3.29, 1.10, 0.00],[3.49, 1.10, 0.00],[3.68, 1.10, 0.00],[3.87, 1.10, 0.00]
    ],
    [
        [0.00, 1.20, 0.00],[0.19, 1.20, 0.00],[0.38, 1.20, 0.00],[0.57, 1.20, 0.00],[0.77, 1.20, 0.00],[0.96, 1.20, 0.00],[1.15, 1.20, 0.00],[1.34, 1.20, 0.00],[1.53, 1.20, 0.00],[1.72, 1.20, 0.00],[1.91, 1.20, 0.00],[2.10, 1.20, 0.00],[2.30, 1.20, 0.00],[2.49, 1.20, 0.00],[2.68, 1.20, 0.00],[2.87, 1.20, 0.00],[3.06, 1.20, 0.00],[3.25, 1.20, 0.00],[3.44, 1.20, 0.00],[3.64, 1.20, 0.00],[3.83, 1.20, 0.00]
    ],
    [
        [0.00, 1.30, 0.00],[0.19, 1.30, 0.00],[0.38, 1.30, 0.00],[0.57, 1.30, 0.00],[0.75, 1.30, 0.00],[0.94, 1.30, 0.00],[1.13, 1.30, 0.00],[1.32, 1.30, 0.00],[1.51, 1.30, 0.00],[1.70, 1.30, 0.00],[1.88, 1.30, 0.00],[2.07, 1.30, 0.00],[2.26, 1.30, 0.00],[2.45, 1.30, 0.00],[2.64, 1.30, 0.00],[2.83, 1.30, 0.00],[3.02, 1.30, 0.00],[3.20, 1.30, 0.00],[3.39, 1.30, 0.00],[3.58, 1.30, 0.00],[3.77, 1.30, 0.00]
    ],
    [
        [0.00, 1.40, 0.00],[0.19, 1.40, 0.00],[0.37, 1.40, 0.00],[0.56, 1.40, 0.00],[0.74, 1.40, 0.00],[0.93, 1.40, 0.00],[1.11, 1.40, 0.00],[1.30, 1.40, 0.00],[1.48, 1.40, 0.00],[1.67, 1.40, 0.00],[1.85, 1.40, 0.00],[2.04, 1.40, 0.00],[2.22, 1.40, 0.00],[2.41, 1.40, 0.00],[2.59, 1.40, 0.00],[2.78, 1.40, 0.00],[2.96, 1.40, 0.00],[3.15, 1.40, 0.00],[3.33, 1.40, 0.00],[3.52, 1.40, 0.00],[3.70, 1.40, 0.00]
    ],
    [
        [0.00, 1.50, 0.00],[0.18, 1.50, 0.00],[0.36, 1.50, 0.00],[0.54, 1.50, 0.00],[0.72, 1.50, 0.00],[0.90, 1.50, 0.00],[1.09, 1.50, 0.00],[1.27, 1.50, 0.00],[1.45, 1.50, 0.00],[1.63, 1.50, 0.00],[1.81, 1.50, 0.00],[1.99, 1.50, 0.00],[2.17, 1.50, 0.00],[2.35, 1.50, 0.00],[2.53, 1.50, 0.00],[2.71, 1.50, 0.00],[2.89, 1.50, 0.00],[3.08, 1.50, 0.00],[3.26, 1.50, 0.00],[3.44, 1.50, 0.00],[3.62, 1.50, 0.00]
    ],
    [
        [0.00, 1.60, 0.00],[0.18, 1.60, 0.00],[0.35, 1.60, 0.00],[0.53, 1.60, 0.00],[0.70, 1.60, 0.00],[0.88, 1.60, 0.00],[1.06, 1.60, 0.00],[1.23, 1.60, 0.00],[1.41, 1.60, 0.00],[1.58, 1.60, 0.00],[1.76, 1.60, 0.00],[1.94, 1.60, 0.00],[2.11, 1.60, 0.00],[2.29, 1.60, 0.00],[2.46, 1.60, 0.00],[2.64, 1.60, 0.00],[2.82, 1.60, 0.00],[2.99, 1.60, 0.00],[3.17, 1.60, 0.00],[3.34, 1.60, 0.00],[3.52, 1.60, 0.00]
    ],
    [
        [0.00, 1.70, 0.00],[0.17, 1.70, 0.00],[0.34, 1.70, 0.00],[0.51, 1.70, 0.00],[0.68, 1.70, 0.00],[0.85, 1.70, 0.00],[1.02, 1.70, 0.00],[1.19, 1.70, 0.00],[1.36, 1.70, 0.00],[1.53, 1.70, 0.00],[1.70, 1.70, 0.00],[1.87, 1.70, 0.00],[2.04, 1.70, 0.00],[2.21, 1.70, 0.00],[2.38, 1.70, 0.00],[2.55, 1.70, 0.00],[2.72, 1.70, 0.00],[2.89, 1.70, 0.00],[3.06, 1.70, 0.00],[3.23, 1.70, 0.00],[3.40, 1.70, 0.00]
    ],
    [
        [0.00, 1.80, 0.00],[0.16, 1.80, 0.00],[0.32, 1.80, 0.00],[0.49, 1.80, 0.00],[0.65, 1.80, 0.00],[0.81, 1.80, 0.00],[0.97, 1.80, 0.00],[1.14, 1.80, 0.00],[1.30, 1.80, 0.00],[1.46, 1.80, 0.00],[1.62, 1.80, 0.00],[1.79, 1.80, 0.00],[1.95, 1.80, 0.00],[2.11, 1.80, 0.00],[2.27, 1.80, 0.00],[2.44, 1.80, 0.00],[2.60, 1.80, 0.00],[2.76, 1.80, 0.00],[2.92, 1.80, 0.00],[3.09, 1.80, 0.00],[3.25, 1.80, 0.00]
    ],
    [
        [0.00, 1.90, 0.00],[0.15, 1.90, 0.00],[0.30, 1.90, 0.00],[0.46, 1.90, 0.00],[0.61, 1.90, 0.00],[0.76, 1.90, 0.00],[0.91, 1.90, 0.00],[1.06, 1.90, 0.00],[1.22, 1.90, 0.00],[1.37, 1.90, 0.00],[1.52, 1.90, 0.00],[1.67, 1.90, 0.00],[1.82, 1.90, 0.00],[1.98, 1.90, 0.00],[2.13, 1.90, 0.00],[2.28, 1.90, 0.00],[2.43, 1.90, 0.00],[2.58, 1.90, 0.00],[2.73, 1.90, 0.00],[2.89, 1.90, 0.00],[3.04, 1.90, 0.00]
    ],
    [
        [0.00, 2.00, 0.00],[0.12, 2.00, 0.00],[0.25, 2.00, 0.00],[0.38, 2.00, 0.00],[0.50, 2.00, 0.00],[0.62, 2.00, 0.00],[0.75, 2.00, 0.00],[0.88, 2.00, 0.00],[1.00, 2.00, 0.00],[1.12, 2.00, 0.00],[1.25, 2.00, 0.00],[1.38, 2.00, 0.00],[1.50, 2.00, 0.00],[1.62, 2.00, 0.00],[1.75, 2.00, 0.00],[1.88, 2.00, 0.00],[2.00, 2.00, 0.00],[2.12, 2.00, 0.00],[2.25, 2.00, 0.00],[2.38, 2.00, 0.00],[2.50, 2.00, 0.00]
    ]
];
