rblack42/math-magik-lpp/mmdesigner/stab_center_cover_points.scad

g_pts = [
    [
        [0.00, 0.00, -0.00],[0.00, 0.30, -0.00],[0.00, 0.60, -0.00],[0.00, 0.90, -0.00],[0.00, 1.20, -0.00],[0.00, 1.50, -0.00],[0.00, 1.80, -0.00],[0.00, 2.10, -0.00],[0.00, 2.40, -0.00],[0.00, 2.70, -0.00],[0.00, 3.00, -0.00],[0.00, 3.30, -0.00],[0.00, 3.60, -0.00],[0.00, 3.90, -0.00],[0.00, 4.20, -0.00],[0.00, 4.50, -0.00],[0.00, 4.80, -0.00],[0.00, 5.10, -0.00],[0.00, 5.40, -0.00],[0.00, 5.70, -0.00],[0.00, 6.00, -0.00]
    ],
    [
        [0.20, 0.00, 0.02],[0.20, 0.30, 0.02],[0.20, 0.60, 0.02],[0.20, 0.90, 0.02],[0.20, 1.20, 0.02],[0.20, 1.50, 0.02],[0.20, 1.80, 0.02],[0.20, 2.10, 0.02],[0.20, 2.40, 0.02],[0.20, 2.70, 0.02],[0.20, 3.00, 0.02],[0.20, 3.30, 0.02],[0.20, 3.60, 0.02],[0.20, 3.90, 0.02],[0.20, 4.20, 0.02],[0.20, 4.50, 0.02],[0.20, 4.80, 0.02],[0.20, 5.10, 0.02],[0.20, 5.40, 0.02],[0.20, 5.70, 0.02],[0.20, 6.00, 0.02]
    ],
    [
        [0.40, 0.00, 0.03],[0.40, 0.30, 0.03],[0.40, 0.60, 0.03],[0.40, 0.90, 0.03],[0.40, 1.20, 0.03],[0.40, 1.50, 0.03],[0.40, 1.80, 0.03],[0.40, 2.10, 0.03],[0.40, 2.40, 0.03],[0.40, 2.70, 0.03],[0.40, 3.00, 0.03],[0.40, 3.30, 0.03],[0.40, 3.60, 0.03],[0.40, 3.90, 0.03],[0.40, 4.20, 0.03],[0.40, 4.50, 0.03],[0.40, 4.80, 0.03],[0.40, 5.10, 0.03],[0.40, 5.40, 0.03],[0.40, 5.70, 0.03],[0.40, 6.00, 0.03]
    ],
    [
        [0.60, 0.00, 0.04],[0.60, 0.30, 0.04],[0.60, 0.60, 0.04],[0.60, 0.90, 0.04],[0.60, 1.20, 0.04],[0.60, 1.50, 0.04],[0.60, 1.80, 0.04],[0.60, 2.10, 0.04],[0.60, 2.40, 0.04],[0.60, 2.70, 0.04],[0.60, 3.00, 0.04],[0.60, 3.30, 0.04],[0.60, 3.60, 0.04],[0.60, 3.90, 0.04],[0.60, 4.20, 0.04],[0.60, 4.50, 0.04],[0.60, 4.80, 0.04],[0.60, 5.10, 0.04],[0.60, 5.40, 0.04],[0.60, 5.70, 0.04],[0.60, 6.00, 0.04]
    ],
    [
        [0.80, 0.00, 0.05],[0.80, 0.30, 0.05],[0.80, 0.60, 0.05],[0.80, 0.90, 0.05],[0.80, 1.20, 0.05],[0.80, 1.50, 0.05],[0.80, 1.80, 0.05],[0.80, 2.10, 0.05],[0.80, 2.40, 0.05],[0.80, 2.70, 0.05],[0.80, 3.00, 0.05],[0.80, 3.30, 0.05],[0.80, 3.60, 0.05],[0.80, 3.90, 0.05],[0.80, 4.20, 0.05],[0.80, 4.50, 0.05],[0.80, 4.80, 0.05],[0.80, 5.10, 0.05],[0.80, 5.40, 0.05],[0.80, 5.70, 0.05],[0.80, 6.00, 0.05]
    ],
    [
        [1.00, 0.00, 0.06],[1.00, 0.30, 0.06],[1.00, 0.60, 0.06],[1.00, 0.90, 0.06],[1.00, 1.20, 0.06],[1.00, 1.50, 0.06],[1.00, 1.80, 0.06],[1.00, 2.10, 0.06],[1.00, 2.40, 0.06],[1.00, 2.70, 0.06],[1.00, 3.00, 0.06],[1.00, 3.30, 0.06],[1.00, 3.60, 0.06],[1.00, 3.90, 0.06],[1.00, 4.20, 0.06],[1.00, 4.50, 0.06],[1.00, 4.80, 0.06],[1.00, 5.10, 0.06],[1.00, 5.40, 0.06],[1.00, 5.70, 0.06],[1.00, 6.00, 0.06]
    ],
    [
        [1.20, 0.00, 0.07],[1.20, 0.30, 0.07],[1.20, 0.60, 0.07],[1.20, 0.90, 0.07],[1.20, 1.20, 0.07],[1.20, 1.50, 0.07],[1.20, 1.80, 0.07],[1.20, 2.10, 0.07],[1.20, 2.40, 0.07],[1.20, 2.70, 0.07],[1.20, 3.00, 0.07],[1.20, 3.30, 0.07],[1.20, 3.60, 0.07],[1.20, 3.90, 0.07],[1.20, 4.20, 0.07],[1.20, 4.50, 0.07],[1.20, 4.80, 0.07],[1.20, 5.10, 0.07],[1.20, 5.40, 0.07],[1.20, 5.70, 0.07],[1.20, 6.00, 0.07]
    ],
    [
        [1.40, 0.00, 0.07],[1.40, 0.30, 0.07],[1.40, 0.60, 0.07],[1.40, 0.90, 0.07],[1.40, 1.20, 0.07],[1.40, 1.50, 0.07],[1.40, 1.80, 0.07],[1.40, 2.10, 0.07],[1.40, 2.40, 0.07],[1.40, 2.70, 0.07],[1.40, 3.00, 0.07],[1.40, 3.30, 0.07],[1.40, 3.60, 0.07],[1.40, 3.90, 0.07],[1.40, 4.20, 0.07],[1.40, 4.50, 0.07],[1.40, 4.80, 0.07],[1.40, 5.10, 0.07],[1.40, 5.40, 0.07],[1.40, 5.70, 0.07],[1.40, 6.00, 0.07]
    ],
    [
        [1.60, 0.00, 0.08],[1.60, 0.30, 0.08],[1.60, 0.60, 0.08],[1.60, 0.90, 0.08],[1.60, 1.20, 0.08],[1.60, 1.50, 0.08],[1.60, 1.80, 0.08],[1.60, 2.10, 0.08],[1.60, 2.40, 0.08],[1.60, 2.70, 0.08],[1.60, 3.00, 0.08],[1.60, 3.30, 0.08],[1.60, 3.60, 0.08],[1.60, 3.90, 0.08],[1.60, 4.20, 0.08],[1.60, 4.50, 0.08],[1.60, 4.80, 0.08],[1.60, 5.10, 0.08],[1.60, 5.40, 0.08],[1.60, 5.70, 0.08],[1.60, 6.00, 0.08]
    ],
    [
        [1.80, 0.00, 0.08],[1.80, 0.30, 0.08],[1.80, 0.60, 0.08],[1.80, 0.90, 0.08],[1.80, 1.20, 0.08],[1.80, 1.50, 0.08],[1.80, 1.80, 0.08],[1.80, 2.10, 0.08],[1.80, 2.40, 0.08],[1.80, 2.70, 0.08],[1.80, 3.00, 0.08],[1.80, 3.30, 0.08],[1.80, 3.60, 0.08],[1.80, 3.90, 0.08],[1.80, 4.20, 0.08],[1.80, 4.50, 0.08],[1.80, 4.80, 0.08],[1.80, 5.10, 0.08],[1.80, 5.40, 0.08],[1.80, 5.70, 0.08],[1.80, 6.00, 0.08]
    ],
    [
        [2.00, 0.00, 0.08],[2.00, 0.30, 0.08],[2.00, 0.60, 0.08],[2.00, 0.90, 0.08],[2.00, 1.20, 0.08],[2.00, 1.50, 0.08],[2.00, 1.80, 0.08],[2.00, 2.10, 0.08],[2.00, 2.40, 0.08],[2.00, 2.70, 0.08],[2.00, 3.00, 0.08],[2.00, 3.30, 0.08],[2.00, 3.60, 0.08],[2.00, 3.90, 0.08],[2.00, 4.20, 0.08],[2.00, 4.50, 0.08],[2.00, 4.80, 0.08],[2.00, 5.10, 0.08],[2.00, 5.40, 0.08],[2.00, 5.70, 0.08],[2.00, 6.00, 0.08]
    ],
    [
        [2.20, 0.00, 0.08],[2.20, 0.30, 0.08],[2.20, 0.60, 0.08],[2.20, 0.90, 0.08],[2.20, 1.20, 0.08],[2.20, 1.50, 0.08],[2.20, 1.80, 0.08],[2.20, 2.10, 0.08],[2.20, 2.40, 0.08],[2.20, 2.70, 0.08],[2.20, 3.00, 0.08],[2.20, 3.30, 0.08],[2.20, 3.60, 0.08],[2.20, 3.90, 0.08],[2.20, 4.20, 0.08],[2.20, 4.50, 0.08],[2.20, 4.80, 0.08],[2.20, 5.10, 0.08],[2.20, 5.40, 0.08],[2.20, 5.70, 0.08],[2.20, 6.00, 0.08]
    ],
    [
        [2.40, 0.00, 0.08],[2.40, 0.30, 0.08],[2.40, 0.60, 0.08],[2.40, 0.90, 0.08],[2.40, 1.20, 0.08],[2.40, 1.50, 0.08],[2.40, 1.80, 0.08],[2.40, 2.10, 0.08],[2.40, 2.40, 0.08],[2.40, 2.70, 0.08],[2.40, 3.00, 0.08],[2.40, 3.30, 0.08],[2.40, 3.60, 0.08],[2.40, 3.90, 0.08],[2.40, 4.20, 0.08],[2.40, 4.50, 0.08],[2.40, 4.80, 0.08],[2.40, 5.10, 0.08],[2.40, 5.40, 0.08],[2.40, 5.70, 0.08],[2.40, 6.00, 0.08]
    ],
    [
        [2.60, 0.00, 0.07],[2.60, 0.30, 0.07],[2.60, 0.60, 0.07],[2.60, 0.90, 0.07],[2.60, 1.20, 0.07],[2.60, 1.50, 0.07],[2.60, 1.80, 0.07],[2.60, 2.10, 0.07],[2.60, 2.40, 0.07],[2.60, 2.70, 0.07],[2.60, 3.00, 0.07],[2.60, 3.30, 0.07],[2.60, 3.60, 0.07],[2.60, 3.90, 0.07],[2.60, 4.20, 0.07],[2.60, 4.50, 0.07],[2.60, 4.80, 0.07],[2.60, 5.10, 0.07],[2.60, 5.40, 0.07],[2.60, 5.70, 0.07],[2.60, 6.00, 0.07]
    ],
    [
        [2.80, 0.00, 0.07],[2.80, 0.30, 0.07],[2.80, 0.60, 0.07],[2.80, 0.90, 0.07],[2.80, 1.20, 0.07],[2.80, 1.50, 0.07],[2.80, 1.80, 0.07],[2.80, 2.10, 0.07],[2.80, 2.40, 0.07],[2.80, 2.70, 0.07],[2.80, 3.00, 0.07],[2.80, 3.30, 0.07],[2.80, 3.60, 0.07],[2.80, 3.90, 0.07],[2.80, 4.20, 0.07],[2.80, 4.50, 0.07],[2.80, 4.80, 0.07],[2.80, 5.10, 0.07],[2.80, 5.40, 0.07],[2.80, 5.70, 0.07],[2.80, 6.00, 0.07]
    ],
    [
        [3.00, 0.00, 0.06],[3.00, 0.30, 0.06],[3.00, 0.60, 0.06],[3.00, 0.90, 0.06],[3.00, 1.20, 0.06],[3.00, 1.50, 0.06],[3.00, 1.80, 0.06],[3.00, 2.10, 0.06],[3.00, 2.40, 0.06],[3.00, 2.70, 0.06],[3.00, 3.00, 0.06],[3.00, 3.30, 0.06],[3.00, 3.60, 0.06],[3.00, 3.90, 0.06],[3.00, 4.20, 0.06],[3.00, 4.50, 0.06],[3.00, 4.80, 0.06],[3.00, 5.10, 0.06],[3.00, 5.40, 0.06],[3.00, 5.70, 0.06],[3.00, 6.00, 0.06]
    ],
    [
        [3.20, 0.00, 0.05],[3.20, 0.30, 0.05],[3.20, 0.60, 0.05],[3.20, 0.90, 0.05],[3.20, 1.20, 0.05],[3.20, 1.50, 0.05],[3.20, 1.80, 0.05],[3.20, 2.10, 0.05],[3.20, 2.40, 0.05],[3.20, 2.70, 0.05],[3.20, 3.00, 0.05],[3.20, 3.30, 0.05],[3.20, 3.60, 0.05],[3.20, 3.90, 0.05],[3.20, 4.20, 0.05],[3.20, 4.50, 0.05],[3.20, 4.80, 0.05],[3.20, 5.10, 0.05],[3.20, 5.40, 0.05],[3.20, 5.70, 0.05],[3.20, 6.00, 0.05]
    ],
    [
        [3.40, 0.00, 0.04],[3.40, 0.30, 0.04],[3.40, 0.60, 0.04],[3.40, 0.90, 0.04],[3.40, 1.20, 0.04],[3.40, 1.50, 0.04],[3.40, 1.80, 0.04],[3.40, 2.10, 0.04],[3.40, 2.40, 0.04],[3.40, 2.70, 0.04],[3.40, 3.00, 0.04],[3.40, 3.30, 0.04],[3.40, 3.60, 0.04],[3.40, 3.90, 0.04],[3.40, 4.20, 0.04],[3.40, 4.50, 0.04],[3.40, 4.80, 0.04],[3.40, 5.10, 0.04],[3.40, 5.40, 0.04],[3.40, 5.70, 0.04],[3.40, 6.00, 0.04]
    ],
    [
        [3.60, 0.00, 0.03],[3.60, 0.30, 0.03],[3.60, 0.60, 0.03],[3.60, 0.90, 0.03],[3.60, 1.20, 0.03],[3.60, 1.50, 0.03],[3.60, 1.80, 0.03],[3.60, 2.10, 0.03],[3.60, 2.40, 0.03],[3.60, 2.70, 0.03],[3.60, 3.00, 0.03],[3.60, 3.30, 0.03],[3.60, 3.60, 0.03],[3.60, 3.90, 0.03],[3.60, 4.20, 0.03],[3.60, 4.50, 0.03],[3.60, 4.80, 0.03],[3.60, 5.10, 0.03],[3.60, 5.40, 0.03],[3.60, 5.70, 0.03],[3.60, 6.00, 0.03]
    ],
    [
        [3.80, 0.00, 0.02],[3.80, 0.30, 0.02],[3.80, 0.60, 0.02],[3.80, 0.90, 0.02],[3.80, 1.20, 0.02],[3.80, 1.50, 0.02],[3.80, 1.80, 0.02],[3.80, 2.10, 0.02],[3.80, 2.40, 0.02],[3.80, 2.70, 0.02],[3.80, 3.00, 0.02],[3.80, 3.30, 0.02],[3.80, 3.60, 0.02],[3.80, 3.90, 0.02],[3.80, 4.20, 0.02],[3.80, 4.50, 0.02],[3.80, 4.80, 0.02],[3.80, 5.10, 0.02],[3.80, 5.40, 0.02],[3.80, 5.70, 0.02],[3.80, 6.00, 0.02]
    ],
    [
        [4.00, 0.00, -0.00],[4.00, 0.30, -0.00],[4.00, 0.60, -0.00],[4.00, 0.90, -0.00],[4.00, 1.20, -0.00],[4.00, 1.50, -0.00],[4.00, 1.80, -0.00],[4.00, 2.10, -0.00],[4.00, 2.40, -0.00],[4.00, 2.70, -0.00],[4.00, 3.00, -0.00],[4.00, 3.30, -0.00],[4.00, 3.60, -0.00],[4.00, 3.90, -0.00],[4.00, 4.20, -0.00],[4.00, 4.50, -0.00],[4.00, 4.80, -0.00],[4.00, 5.10, -0.00],[4.00, 5.40, -0.00],[4.00, 5.70, -0.00],[4.00, 6.00, -0.00]
    ]
];
