rblack42/math-magik-lpp/mmdesigner/stab_tip_cover_points.scad

g_pts = [
    [
        [0.00, 0.00, 0.00],[0.20, 0.00, 0.00],[0.40, 0.00, 0.00],[0.60, 0.00, 0.00],[0.80, 0.00, 0.00],[1.00, 0.00, 0.00],[1.20, 0.00, 0.00],[1.40, 0.00, 0.00],[1.60, 0.00, 0.00],[1.80, 0.00, 0.00],[2.00, 0.00, 0.00],[2.20, 0.00, 0.00],[2.40, 0.00, 0.00],[2.60, 0.00, 0.00],[2.80, 0.00, 0.00],[3.00, 0.00, 0.00],[3.20, 0.00, 0.00],[3.40, 0.00, 0.00],[3.60, 0.00, 0.00],[3.80, 0.00, 0.00],[4.00, 0.00, 0.00]
    ],
    [
        [0.00, 0.15, 0.00],[0.20, 0.15, 0.00],[0.40, 0.15, 0.00],[0.60, 0.15, 0.00],[0.80, 0.15, 0.00],[1.00, 0.15, 0.00],[1.20, 0.15, 0.00],[1.40, 0.15, 0.00],[1.60, 0.15, 0.00],[1.80, 0.15, 0.00],[2.00, 0.15, 0.00],[2.20, 0.15, 0.00],[2.40, 0.15, 0.00],[2.60, 0.15, 0.00],[2.80, 0.15, 0.00],[3.00, 0.15, 0.00],[3.20, 0.15, 0.00],[3.40, 0.15, 0.00],[3.60, 0.15, 0.00],[3.80, 0.15, 0.00],[4.00, 0.15, 0.00]
    ],
    [
        [0.00, 0.30, 0.00],[0.20, 0.30, 0.00],[0.40, 0.30, 0.00],[0.60, 0.30, 0.00],[0.80, 0.30, 0.00],[1.00, 0.30, 0.00],[1.20, 0.30, 0.00],[1.40, 0.30, 0.00],[1.60, 0.30, 0.00],[1.80, 0.30, 0.00],[2.00, 0.30, 0.00],[2.20, 0.30, 0.00],[2.40, 0.30, 0.00],[2.60, 0.30, 0.00],[2.80, 0.30, 0.00],[3.00, 0.30, 0.00],[3.20, 0.30, 0.00],[3.40, 0.30, 0.00],[3.60, 0.30, 0.00],[3.80, 0.30, 0.00],[4.00, 0.30, 0.00]
    ],
    [
        [0.00, 0.45, 0.00],[0.20, 0.45, 0.00],[0.40, 0.45, 0.00],[0.60, 0.45, 0.00],[0.80, 0.45, 0.00],[1.00, 0.45, 0.00],[1.20, 0.45, 0.00],[1.40, 0.45, 0.00],[1.60, 0.45, 0.00],[1.80, 0.45, 0.00],[2.00, 0.45, 0.00],[2.20, 0.45, 0.00],[2.40, 0.45, 0.00],[2.60, 0.45, 0.00],[2.80, 0.45, 0.00],[3.00, 0.45, 0.00],[3.20, 0.45, 0.00],[3.40, 0.45, 0.00],[3.60, 0.45, 0.00],[3.80, 0.45, 0.00],[4.00, 0.45, 0.00]
    ],
    [
        [0.00, 0.60, 0.00],[0.20, 0.60, 0.00],[0.40, 0.60, 0.00],[0.60, 0.60, 0.00],[0.80, 0.60, 0.00],[1.00, 0.60, 0.00],[1.20, 0.60, 0.00],[1.40, 0.60, 0.00],[1.60, 0.60, 0.00],[1.80, 0.60, 0.00],[2.00, 0.60, 0.00],[2.20, 0.60, 0.00],[2.40, 0.60, 0.00],[2.60, 0.60, 0.00],[2.80, 0.60, 0.00],[3.00, 0.60, 0.00],[3.20, 0.60, 0.00],[3.40, 0.60, 0.00],[3.60, 0.60, 0.00],[3.80, 0.60, 0.00],[4.00, 0.60, 0.00]
    ],
    [
        [0.00, 0.75, 0.00],[0.20, 0.75, 0.00],[0.40, 0.75, 0.00],[0.60, 0.75, 0.00],[0.80, 0.75, 0.00],[1.00, 0.75, 0.00],[1.20, 0.75, 0.00],[1.40, 0.75, 0.00],[1.60, 0.75, 0.00],[1.80, 0.75, 0.00],[2.00, 0.75, 0.00],[2.20, 0.75, 0.00],[2.40, 0.75, 0.00],[2.60, 0.75, 0.00],[2.80, 0.75, 0.00],[3.00, 0.75, 0.00],[3.20, 0.75, 0.00],[3.40, 0.75, 0.00],[3.60, 0.75, 0.00],[3.80, 0.75, 0.00],[4.00, 0.75, 0.00]
    ],
    [
        [0.00, 0.90, 0.00],[0.20, 0.90, 0.00],[0.40, 0.90, 0.00],[0.60, 0.90, 0.00],[0.80, 0.90, 0.00],[1.00, 0.90, 0.00],[1.20, 0.90, 0.00],[1.40, 0.90, 0.00],[1.60, 0.90, 0.00],[1.80, 0.90, 0.00],[2.00, 0.90, 0.00],[2.20, 0.90, 0.00],[2.40, 0.90, 0.00],[2.60, 0.90, 0.00],[2.80, 0.90, 0.00],[3.00, 0.90, 0.00],[3.20, 0.90, 0.00],[3.40, 0.90, 0.00],[3.60, 0.90, 0.00],[3.80, 0.90, 0.00],[4.00, 0.90, 0.00]
    ],
    [
        [0.00, 1.05, 0.00],[0.20, 1.05, 0.00],[0.40, 1.05, 0.00],[0.60, 1.05, 0.00],[0.80, 1.05, 0.00],[1.00, 1.05, 0.00],[1.20, 1.05, 0.00],[1.40, 1.05, 0.00],[1.60, 1.05, 0.00],[1.80, 1.05, 0.00],[2.00, 1.05, 0.00],[2.20, 1.05, 0.00],[2.40, 1.05, 0.00],[2.60, 1.05, 0.00],[2.80, 1.05, 0.00],[3.00, 1.05, 0.00],[3.20, 1.05, 0.00],[3.40, 1.05, 0.00],[3.60, 1.05, 0.00],[3.80, 1.05, 0.00],[4.00, 1.05, 0.00]
    ],
    [
        [0.00, 1.20, 0.00],[0.20, 1.20, 0.00],[0.40, 1.20, 0.00],[0.60, 1.20, 0.00],[0.80, 1.20, 0.00],[1.00, 1.20, 0.00],[1.20, 1.20, 0.00],[1.40, 1.20, 0.00],[1.60, 1.20, 0.00],[1.80, 1.20, 0.00],[2.00, 1.20, 0.00],[2.20, 1.20, 0.00],[2.40, 1.20, 0.00],[2.60, 1.20, 0.00],[2.80, 1.20, 0.00],[3.00, 1.20, 0.00],[3.20, 1.20, 0.00],[3.40, 1.20, 0.00],[3.60, 1.20, 0.00],[3.80, 1.20, 0.00],[4.00, 1.20, 0.00]
    ],
    [
        [0.00, 1.35, 0.00],[0.20, 1.35, 0.00],[0.40, 1.35, 0.00],[0.60, 1.35, 0.00],[0.80, 1.35, 0.00],[1.00, 1.35, 0.00],[1.20, 1.35, 0.00],[1.40, 1.35, 0.00],[1.60, 1.35, 0.00],[1.80, 1.35, 0.00],[2.00, 1.35, 0.00],[2.20, 1.35, 0.00],[2.40, 1.35, 0.00],[2.60, 1.35, 0.00],[2.80, 1.35, 0.00],[3.00, 1.35, 0.00],[3.20, 1.35, 0.00],[3.40, 1.35, 0.00],[3.60, 1.35, 0.00],[3.80, 1.35, 0.00],[4.00, 1.35, 0.00]
    ],
    [
        [0.00, 1.50, 0.00],[0.20, 1.50, 0.00],[0.40, 1.50, 0.00],[0.60, 1.50, 0.00],[0.80, 1.50, 0.00],[1.00, 1.50, 0.00],[1.20, 1.50, 0.00],[1.40, 1.50, 0.00],[1.60, 1.50, 0.00],[1.80, 1.50, 0.00],[2.00, 1.50, 0.00],[2.20, 1.50, 0.00],[2.40, 1.50, 0.00],[2.60, 1.50, 0.00],[2.80, 1.50, 0.00],[3.00, 1.50, 0.00],[3.20, 1.50, 0.00],[3.40, 1.50, 0.00],[3.60, 1.50, 0.00],[3.80, 1.50, 0.00],[4.00, 1.50, 0.00]
    ],
    [
        [0.00, 1.65, 0.00],[0.20, 1.65, 0.00],[0.40, 1.65, 0.00],[0.60, 1.65, 0.00],[0.80, 1.65, 0.00],[1.00, 1.65, 0.00],[1.20, 1.65, 0.00],[1.40, 1.65, 0.00],[1.60, 1.65, 0.00],[1.80, 1.65, 0.00],[2.00, 1.65, 0.00],[2.20, 1.65, 0.00],[2.40, 1.65, 0.00],[2.60, 1.65, 0.00],[2.79, 1.65, 0.00],[2.99, 1.65, 0.00],[3.19, 1.65, 0.00],[3.39, 1.65, 0.00],[3.59, 1.65, 0.00],[3.79, 1.65, 0.00],[3.99, 1.65, 0.00]
    ],
    [
        [0.00, 1.80, 0.00],[0.20, 1.80, 0.00],[0.40, 1.80, 0.00],[0.60, 1.80, 0.00],[0.79, 1.80, 0.00],[0.99, 1.80, 0.00],[1.19, 1.80, 0.00],[1.39, 1.80, 0.00],[1.59, 1.80, 0.00],[1.79, 1.80, 0.00],[1.98, 1.80, 0.00],[2.18, 1.80, 0.00],[2.38, 1.80, 0.00],[2.58, 1.80, 0.00],[2.78, 1.80, 0.00],[2.98, 1.80, 0.00],[3.18, 1.80, 0.00],[3.37, 1.80, 0.00],[3.57, 1.80, 0.00],[3.77, 1.80, 0.00],[3.97, 1.80, 0.00]
    ],
    [
        [0.00, 1.95, 0.00],[0.20, 1.95, 0.00],[0.39, 1.95, 0.00],[0.59, 1.95, 0.00],[0.79, 1.95, 0.00],[0.98, 1.95, 0.00],[1.18, 1.95, 0.00],[1.38, 1.95, 0.00],[1.57, 1.95, 0.00],[1.77, 1.95, 0.00],[1.97, 1.95, 0.00],[2.16, 1.95, 0.00],[2.36, 1.95, 0.00],[2.56, 1.95, 0.00],[2.75, 1.95, 0.00],[2.95, 1.95, 0.00],[3.14, 1.95, 0.00],[3.34, 1.95, 0.00],[3.54, 1.95, 0.00],[3.73, 1.95, 0.00],[3.93, 1.95, 0.00]
    ],
    [
        [0.00, 2.10, 0.00],[0.19, 2.10, 0.00],[0.39, 2.10, 0.00],[0.58, 2.10, 0.00],[0.77, 2.10, 0.00],[0.97, 2.10, 0.00],[1.16, 2.10, 0.00],[1.36, 2.10, 0.00],[1.55, 2.10, 0.00],[1.74, 2.10, 0.00],[1.94, 2.10, 0.00],[2.13, 2.10, 0.00],[2.32, 2.10, 0.00],[2.52, 2.10, 0.00],[2.71, 2.10, 0.00],[2.91, 2.10, 0.00],[3.10, 2.10, 0.00],[3.29, 2.10, 0.00],[3.49, 2.10, 0.00],[3.68, 2.10, 0.00],[3.87, 2.10, 0.00]
    ],
    [
        [0.00, 2.25, 0.00],[0.19, 2.25, 0.00],[0.38, 2.25, 0.00],[0.57, 2.25, 0.00],[0.76, 2.25, 0.00],[0.95, 2.25, 0.00],[1.14, 2.25, 0.00],[1.33, 2.25, 0.00],[1.52, 2.25, 0.00],[1.71, 2.25, 0.00],[1.90, 2.25, 0.00],[2.09, 2.25, 0.00],[2.28, 2.25, 0.00],[2.47, 2.25, 0.00],[2.66, 2.25, 0.00],[2.85, 2.25, 0.00],[3.04, 2.25, 0.00],[3.23, 2.25, 0.00],[3.42, 2.25, 0.00],[3.61, 2.25, 0.00],[3.80, 2.25, 0.00]
    ],
    [
        [0.00, 2.40, 0.00],[0.18, 2.40, 0.00],[0.37, 2.40, 0.00],[0.56, 2.40, 0.00],[0.74, 2.40, 0.00],[0.92, 2.40, 0.00],[1.11, 2.40, 0.00],[1.29, 2.40, 0.00],[1.48, 2.40, 0.00],[1.66, 2.40, 0.00],[1.85, 2.40, 0.00],[2.04, 2.40, 0.00],[2.22, 2.40, 0.00],[2.40, 2.40, 0.00],[2.59, 2.40, 0.00],[2.77, 2.40, 0.00],[2.96, 2.40, 0.00],[3.15, 2.40, 0.00],[3.33, 2.40, 0.00],[3.52, 2.40, 0.00],[3.70, 2.40, 0.00]
    ],
    [
        [0.00, 2.55, 0.00],[0.18, 2.55, 0.00],[0.36, 2.55, 0.00],[0.54, 2.55, 0.00],[0.71, 2.55, 0.00],[0.89, 2.55, 0.00],[1.07, 2.55, 0.00],[1.25, 2.55, 0.00],[1.43, 2.55, 0.00],[1.61, 2.55, 0.00],[1.79, 2.55, 0.00],[1.96, 2.55, 0.00],[2.14, 2.55, 0.00],[2.32, 2.55, 0.00],[2.50, 2.55, 0.00],[2.68, 2.55, 0.00],[2.86, 2.55, 0.00],[3.04, 2.55, 0.00],[3.21, 2.55, 0.00],[3.39, 2.55, 0.00],[3.57, 2.55, 0.00]
    ],
    [
        [0.00, 2.70, 0.00],[0.17, 2.70, 0.00],[0.34, 2.70, 0.00],[0.51, 2.70, 0.00],[0.68, 2.70, 0.00],[0.85, 2.70, 0.00],[1.02, 2.70, 0.00],[1.19, 2.70, 0.00],[1.36, 2.70, 0.00],[1.53, 2.70, 0.00],[1.70, 2.70, 0.00],[1.87, 2.70, 0.00],[2.04, 2.70, 0.00],[2.21, 2.70, 0.00],[2.38, 2.70, 0.00],[2.55, 2.70, 0.00],[2.72, 2.70, 0.00],[2.89, 2.70, 0.00],[3.06, 2.70, 0.00],[3.23, 2.70, 0.00],[3.40, 2.70, 0.00]
    ],
    [
        [0.00, 2.85, 0.00],[0.16, 2.85, 0.00],[0.32, 2.85, 0.00],[0.47, 2.85, 0.00],[0.63, 2.85, 0.00],[0.79, 2.85, 0.00],[0.95, 2.85, 0.00],[1.10, 2.85, 0.00],[1.26, 2.85, 0.00],[1.42, 2.85, 0.00],[1.58, 2.85, 0.00],[1.73, 2.85, 0.00],[1.89, 2.85, 0.00],[2.05, 2.85, 0.00],[2.21, 2.85, 0.00],[2.37, 2.85, 0.00],[2.52, 2.85, 0.00],[2.68, 2.85, 0.00],[2.84, 2.85, 0.00],[3.00, 2.85, 0.00],[3.15, 2.85, 0.00]
    ],
    [
        [0.00, 3.00, 0.00],[0.12, 3.00, 0.00],[0.25, 3.00, 0.00],[0.38, 3.00, 0.00],[0.50, 3.00, 0.00],[0.62, 3.00, 0.00],[0.75, 3.00, 0.00],[0.88, 3.00, 0.00],[1.00, 3.00, 0.00],[1.12, 3.00, 0.00],[1.25, 3.00, 0.00],[1.38, 3.00, 0.00],[1.50, 3.00, 0.00],[1.62, 3.00, 0.00],[1.75, 3.00, 0.00],[1.88, 3.00, 0.00],[2.00, 3.00, 0.00],[2.12, 3.00, 0.00],[2.25, 3.00, 0.00],[2.38, 3.00, 0.00],[2.50, 3.00, 0.00]
    ]
];
