rblack42/math-magik-lpp/mmdesigner/wing_center_cover_points.scad

g_pts = [
    [
        [0.00, 0.00, -0.00],[0.00, 0.60, -0.00],[0.00, 1.20, -0.00],[0.00, 1.80, -0.00],[0.00, 2.40, -0.00],[0.00, 3.00, -0.00],[0.00, 3.60, -0.00],[0.00, 4.20, -0.00],[0.00, 4.80, -0.00],[0.00, 5.40, -0.00],[0.00, 6.00, -0.00],[0.00, 6.60, -0.00],[0.00, 7.20, -0.00],[0.00, 7.80, -0.00],[0.00, 8.40, -0.00],[0.00, 9.00, -0.00],[0.00, 9.60, -0.00],[0.00, 10.20, -0.00],[0.00, 10.80, -0.00],[0.00, 11.40, -0.00],[0.00, 12.00, -0.00]
    ],
    [
        [0.25, 0.00, 0.04],[0.25, 0.60, 0.04],[0.25, 1.20, 0.04],[0.25, 1.80, 0.04],[0.25, 2.40, 0.04],[0.25, 3.00, 0.04],[0.25, 3.60, 0.04],[0.25, 4.20, 0.04],[0.25, 4.80, 0.04],[0.25, 5.40, 0.04],[0.25, 6.00, 0.04],[0.25, 6.60, 0.04],[0.25, 7.20, 0.04],[0.25, 7.80, 0.04],[0.25, 8.40, 0.04],[0.25, 9.00, 0.04],[0.25, 9.60, 0.04],[0.25, 10.20, 0.04],[0.25, 10.80, 0.04],[0.25, 11.40, 0.04],[0.25, 12.00, 0.04]
    ],
    [
        [0.50, 0.00, 0.07],[0.50, 0.60, 0.07],[0.50, 1.20, 0.07],[0.50, 1.80, 0.07],[0.50, 2.40, 0.07],[0.50, 3.00, 0.07],[0.50, 3.60, 0.07],[0.50, 4.20, 0.07],[0.50, 4.80, 0.07],[0.50, 5.40, 0.07],[0.50, 6.00, 0.07],[0.50, 6.60, 0.07],[0.50, 7.20, 0.07],[0.50, 7.80, 0.07],[0.50, 8.40, 0.07],[0.50, 9.00, 0.07],[0.50, 9.60, 0.07],[0.50, 10.20, 0.07],[0.50, 10.80, 0.07],[0.50, 11.40, 0.07],[0.50, 12.00, 0.07]
    ],
    [
        [0.75, 0.00, 0.10],[0.75, 0.60, 0.10],[0.75, 1.20, 0.10],[0.75, 1.80, 0.10],[0.75, 2.40, 0.10],[0.75, 3.00, 0.10],[0.75, 3.60, 0.10],[0.75, 4.20, 0.10],[0.75, 4.80, 0.10],[0.75, 5.40, 0.10],[0.75, 6.00, 0.10],[0.75, 6.60, 0.10],[0.75, 7.20, 0.10],[0.75, 7.80, 0.10],[0.75, 8.40, 0.10],[0.75, 9.00, 0.10],[0.75, 9.60, 0.10],[0.75, 10.20, 0.10],[0.75, 10.80, 0.10],[0.75, 11.40, 0.10],[0.75, 12.00, 0.10]
    ],
    [
        [1.00, 0.00, 0.13],[1.00, 0.60, 0.13],[1.00, 1.20, 0.13],[1.00, 1.80, 0.13],[1.00, 2.40, 0.13],[1.00, 3.00, 0.13],[1.00, 3.60, 0.13],[1.00, 4.20, 0.13],[1.00, 4.80, 0.13],[1.00, 5.40, 0.13],[1.00, 6.00, 0.13],[1.00, 6.60, 0.13],[1.00, 7.20, 0.13],[1.00, 7.80, 0.13],[1.00, 8.40, 0.13],[1.00, 9.00, 0.13],[1.00, 9.60, 0.13],[1.00, 10.20, 0.13],[1.00, 10.80, 0.13],[1.00, 11.40, 0.13],[1.00, 12.00, 0.13]
    ],
    [
        [1.25, 0.00, 0.15],[1.25, 0.60, 0.15],[1.25, 1.20, 0.15],[1.25, 1.80, 0.15],[1.25, 2.40, 0.15],[1.25, 3.00, 0.15],[1.25, 3.60, 0.15],[1.25, 4.20, 0.15],[1.25, 4.80, 0.15],[1.25, 5.40, 0.15],[1.25, 6.00, 0.15],[1.25, 6.60, 0.15],[1.25, 7.20, 0.15],[1.25, 7.80, 0.15],[1.25, 8.40, 0.15],[1.25, 9.00, 0.15],[1.25, 9.60, 0.15],[1.25, 10.20, 0.15],[1.25, 10.80, 0.15],[1.25, 11.40, 0.15],[1.25, 12.00, 0.15]
    ],
    [
        [1.50, 0.00, 0.17],[1.50, 0.60, 0.17],[1.50, 1.20, 0.17],[1.50, 1.80, 0.17],[1.50, 2.40, 0.17],[1.50, 3.00, 0.17],[1.50, 3.60, 0.17],[1.50, 4.20, 0.17],[1.50, 4.80, 0.17],[1.50, 5.40, 0.17],[1.50, 6.00, 0.17],[1.50, 6.60, 0.17],[1.50, 7.20, 0.17],[1.50, 7.80, 0.17],[1.50, 8.40, 0.17],[1.50, 9.00, 0.17],[1.50, 9.60, 0.17],[1.50, 10.20, 0.17],[1.50, 10.80, 0.17],[1.50, 11.40, 0.17],[1.50, 12.00, 0.17]
    ],
    [
        [1.75, 0.00, 0.18],[1.75, 0.60, 0.18],[1.75, 1.20, 0.18],[1.75, 1.80, 0.18],[1.75, 2.40, 0.18],[1.75, 3.00, 0.18],[1.75, 3.60, 0.18],[1.75, 4.20, 0.18],[1.75, 4.80, 0.18],[1.75, 5.40, 0.18],[1.75, 6.00, 0.18],[1.75, 6.60, 0.18],[1.75, 7.20, 0.18],[1.75, 7.80, 0.18],[1.75, 8.40, 0.18],[1.75, 9.00, 0.18],[1.75, 9.60, 0.18],[1.75, 10.20, 0.18],[1.75, 10.80, 0.18],[1.75, 11.40, 0.18],[1.75, 12.00, 0.18]
    ],
    [
        [2.00, 0.00, 0.19],[2.00, 0.60, 0.19],[2.00, 1.20, 0.19],[2.00, 1.80, 0.19],[2.00, 2.40, 0.19],[2.00, 3.00, 0.19],[2.00, 3.60, 0.19],[2.00, 4.20, 0.19],[2.00, 4.80, 0.19],[2.00, 5.40, 0.19],[2.00, 6.00, 0.19],[2.00, 6.60, 0.19],[2.00, 7.20, 0.19],[2.00, 7.80, 0.19],[2.00, 8.40, 0.19],[2.00, 9.00, 0.19],[2.00, 9.60, 0.19],[2.00, 10.20, 0.19],[2.00, 10.80, 0.19],[2.00, 11.40, 0.19],[2.00, 12.00, 0.19]
    ],
    [
        [2.25, 0.00, 0.20],[2.25, 0.60, 0.20],[2.25, 1.20, 0.20],[2.25, 1.80, 0.20],[2.25, 2.40, 0.20],[2.25, 3.00, 0.20],[2.25, 3.60, 0.20],[2.25, 4.20, 0.20],[2.25, 4.80, 0.20],[2.25, 5.40, 0.20],[2.25, 6.00, 0.20],[2.25, 6.60, 0.20],[2.25, 7.20, 0.20],[2.25, 7.80, 0.20],[2.25, 8.40, 0.20],[2.25, 9.00, 0.20],[2.25, 9.60, 0.20],[2.25, 10.20, 0.20],[2.25, 10.80, 0.20],[2.25, 11.40, 0.20],[2.25, 12.00, 0.20]
    ],
    [
        [2.50, 0.00, 0.20],[2.50, 0.60, 0.20],[2.50, 1.20, 0.20],[2.50, 1.80, 0.20],[2.50, 2.40, 0.20],[2.50, 3.00, 0.20],[2.50, 3.60, 0.20],[2.50, 4.20, 0.20],[2.50, 4.80, 0.20],[2.50, 5.40, 0.20],[2.50, 6.00, 0.20],[2.50, 6.60, 0.20],[2.50, 7.20, 0.20],[2.50, 7.80, 0.20],[2.50, 8.40, 0.20],[2.50, 9.00, 0.20],[2.50, 9.60, 0.20],[2.50, 10.20, 0.20],[2.50, 10.80, 0.20],[2.50, 11.40, 0.20],[2.50, 12.00, 0.20]
    ],
    [
        [2.75, 0.00, 0.20],[2.75, 0.60, 0.20],[2.75, 1.20, 0.20],[2.75, 1.80, 0.20],[2.75, 2.40, 0.20],[2.75, 3.00, 0.20],[2.75, 3.60, 0.20],[2.75, 4.20, 0.20],[2.75, 4.80, 0.20],[2.75, 5.40, 0.20],[2.75, 6.00, 0.20],[2.75, 6.60, 0.20],[2.75, 7.20, 0.20],[2.75, 7.80, 0.20],[2.75, 8.40, 0.20],[2.75, 9.00, 0.20],[2.75, 9.60, 0.20],[2.75, 10.20, 0.20],[2.75, 10.80, 0.20],[2.75, 11.40, 0.20],[2.75, 12.00, 0.20]
    ],
    [
        [3.00, 0.00, 0.19],[3.00, 0.60, 0.19],[3.00, 1.20, 0.19],[3.00, 1.80, 0.19],[3.00, 2.40, 0.19],[3.00, 3.00, 0.19],[3.00, 3.60, 0.19],[3.00, 4.20, 0.19],[3.00, 4.80, 0.19],[3.00, 5.40, 0.19],[3.00, 6.00, 0.19],[3.00, 6.60, 0.19],[3.00, 7.20, 0.19],[3.00, 7.80, 0.19],[3.00, 8.40, 0.19],[3.00, 9.00, 0.19],[3.00, 9.60, 0.19],[3.00, 10.20, 0.19],[3.00, 10.80, 0.19],[3.00, 11.40, 0.19],[3.00, 12.00, 0.19]
    ],
    [
        [3.25, 0.00, 0.18],[3.25, 0.60, 0.18],[3.25, 1.20, 0.18],[3.25, 1.80, 0.18],[3.25, 2.40, 0.18],[3.25, 3.00, 0.18],[3.25, 3.60, 0.18],[3.25, 4.20, 0.18],[3.25, 4.80, 0.18],[3.25, 5.40, 0.18],[3.25, 6.00, 0.18],[3.25, 6.60, 0.18],[3.25, 7.20, 0.18],[3.25, 7.80, 0.18],[3.25, 8.40, 0.18],[3.25, 9.00, 0.18],[3.25, 9.60, 0.18],[3.25, 10.20, 0.18],[3.25, 10.80, 0.18],[3.25, 11.40, 0.18],[3.25, 12.00, 0.18]
    ],
    [
        [3.50, 0.00, 0.17],[3.50, 0.60, 0.17],[3.50, 1.20, 0.17],[3.50, 1.80, 0.17],[3.50, 2.40, 0.17],[3.50, 3.00, 0.17],[3.50, 3.60, 0.17],[3.50, 4.20, 0.17],[3.50, 4.80, 0.17],[3.50, 5.40, 0.17],[3.50, 6.00, 0.17],[3.50, 6.60, 0.17],[3.50, 7.20, 0.17],[3.50, 7.80, 0.17],[3.50, 8.40, 0.17],[3.50, 9.00, 0.17],[3.50, 9.60, 0.17],[3.50, 10.20, 0.17],[3.50, 10.80, 0.17],[3.50, 11.40, 0.17],[3.50, 12.00, 0.17]
    ],
    [
        [3.75, 0.00, 0.15],[3.75, 0.60, 0.15],[3.75, 1.20, 0.15],[3.75, 1.80, 0.15],[3.75, 2.40, 0.15],[3.75, 3.00, 0.15],[3.75, 3.60, 0.15],[3.75, 4.20, 0.15],[3.75, 4.80, 0.15],[3.75, 5.40, 0.15],[3.75, 6.00, 0.15],[3.75, 6.60, 0.15],[3.75, 7.20, 0.15],[3.75, 7.80, 0.15],[3.75, 8.40, 0.15],[3.75, 9.00, 0.15],[3.75, 9.60, 0.15],[3.75, 10.20, 0.15],[3.75, 10.80, 0.15],[3.75, 11.40, 0.15],[3.75, 12.00, 0.15]
    ],
    [
        [4.00, 0.00, 0.13],[4.00, 0.60, 0.13],[4.00, 1.20, 0.13],[4.00, 1.80, 0.13],[4.00, 2.40, 0.13],[4.00, 3.00, 0.13],[4.00, 3.60, 0.13],[4.00, 4.20, 0.13],[4.00, 4.80, 0.13],[4.00, 5.40, 0.13],[4.00, 6.00, 0.13],[4.00, 6.60, 0.13],[4.00, 7.20, 0.13],[4.00, 7.80, 0.13],[4.00, 8.40, 0.13],[4.00, 9.00, 0.13],[4.00, 9.60, 0.13],[4.00, 10.20, 0.13],[4.00, 10.80, 0.13],[4.00, 11.40, 0.13],[4.00, 12.00, 0.13]
    ],
    [
        [4.25, 0.00, 0.10],[4.25, 0.60, 0.10],[4.25, 1.20, 0.10],[4.25, 1.80, 0.10],[4.25, 2.40, 0.10],[4.25, 3.00, 0.10],[4.25, 3.60, 0.10],[4.25, 4.20, 0.10],[4.25, 4.80, 0.10],[4.25, 5.40, 0.10],[4.25, 6.00, 0.10],[4.25, 6.60, 0.10],[4.25, 7.20, 0.10],[4.25, 7.80, 0.10],[4.25, 8.40, 0.10],[4.25, 9.00, 0.10],[4.25, 9.60, 0.10],[4.25, 10.20, 0.10],[4.25, 10.80, 0.10],[4.25, 11.40, 0.10],[4.25, 12.00, 0.10]
    ],
    [
        [4.50, 0.00, 0.07],[4.50, 0.60, 0.07],[4.50, 1.20, 0.07],[4.50, 1.80, 0.07],[4.50, 2.40, 0.07],[4.50, 3.00, 0.07],[4.50, 3.60, 0.07],[4.50, 4.20, 0.07],[4.50, 4.80, 0.07],[4.50, 5.40, 0.07],[4.50, 6.00, 0.07],[4.50, 6.60, 0.07],[4.50, 7.20, 0.07],[4.50, 7.80, 0.07],[4.50, 8.40, 0.07],[4.50, 9.00, 0.07],[4.50, 9.60, 0.07],[4.50, 10.20, 0.07],[4.50, 10.80, 0.07],[4.50, 11.40, 0.07],[4.50, 12.00, 0.07]
    ],
    [
        [4.75, 0.00, 0.04],[4.75, 0.60, 0.04],[4.75, 1.20, 0.04],[4.75, 1.80, 0.04],[4.75, 2.40, 0.04],[4.75, 3.00, 0.04],[4.75, 3.60, 0.04],[4.75, 4.20, 0.04],[4.75, 4.80, 0.04],[4.75, 5.40, 0.04],[4.75, 6.00, 0.04],[4.75, 6.60, 0.04],[4.75, 7.20, 0.04],[4.75, 7.80, 0.04],[4.75, 8.40, 0.04],[4.75, 9.00, 0.04],[4.75, 9.60, 0.04],[4.75, 10.20, 0.04],[4.75, 10.80, 0.04],[4.75, 11.40, 0.04],[4.75, 12.00, 0.04]
    ],
    [
        [5.00, 0.00, -0.00],[5.00, 0.60, -0.00],[5.00, 1.20, -0.00],[5.00, 1.80, -0.00],[5.00, 2.40, -0.00],[5.00, 3.00, -0.00],[5.00, 3.60, -0.00],[5.00, 4.20, -0.00],[5.00, 4.80, -0.00],[5.00, 5.40, -0.00],[5.00, 6.00, -0.00],[5.00, 6.60, -0.00],[5.00, 7.20, -0.00],[5.00, 7.80, -0.00],[5.00, 8.40, -0.00],[5.00, 9.00, -0.00],[5.00, 9.60, -0.00],[5.00, 10.20, -0.00],[5.00, 10.80, -0.00],[5.00, 11.40, -0.00],[5.00, 12.00, -0.00]
    ]
];
