rblack42/math-magik-lpp/mmdesigner/wing_tip_cover_points.scad

g_pts = [
    [
        [0.00, 0.00, 0.00],[0.25, 0.00, 0.00],[0.50, 0.00, 0.00],[0.75, 0.00, 0.00],[1.00, 0.00, 0.00],[1.25, 0.00, 0.00],[1.50, 0.00, 0.00],[1.75, 0.00, 0.00],[2.00, 0.00, 0.00],[2.25, 0.00, 0.00],[2.50, 0.00, 0.00],[2.75, 0.00, 0.00],[3.00, 0.00, 0.00],[3.25, 0.00, 0.00],[3.50, 0.00, 0.00],[3.75, 0.00, 0.00],[4.00, 0.00, 0.00],[4.25, 0.00, 0.00],[4.50, 0.00, 0.00],[4.75, 0.00, 0.00],[5.00, 0.00, 0.00]
    ],
    [
        [0.00, 0.17, 0.00],[0.25, 0.17, 0.00],[0.50, 0.17, 0.00],[0.75, 0.17, 0.00],[1.00, 0.17, 0.00],[1.25, 0.17, 0.00],[1.50, 0.17, 0.00],[1.75, 0.17, 0.00],[2.00, 0.17, 0.00],[2.25, 0.17, 0.00],[2.50, 0.17, 0.00],[2.75, 0.17, 0.00],[3.00, 0.17, 0.00],[3.25, 0.17, 0.00],[3.50, 0.17, 0.00],[3.75, 0.17, 0.00],[4.00, 0.17, 0.00],[4.25, 0.17, 0.00],[4.50, 0.17, 0.00],[4.75, 0.17, 0.00],[5.00, 0.17, 0.00]
    ],
    [
        [0.00, 0.35, 0.00],[0.25, 0.35, 0.00],[0.50, 0.35, 0.00],[0.75, 0.35, 0.00],[1.00, 0.35, 0.00],[1.25, 0.35, 0.00],[1.50, 0.35, 0.00],[1.75, 0.35, 0.00],[2.00, 0.35, 0.00],[2.25, 0.35, 0.00],[2.50, 0.35, 0.00],[2.75, 0.35, 0.00],[3.00, 0.35, 0.00],[3.25, 0.35, 0.00],[3.50, 0.35, 0.00],[3.75, 0.35, 0.00],[4.00, 0.35, 0.00],[4.25, 0.35, 0.00],[4.50, 0.35, 0.00],[4.75, 0.35, 0.00],[5.00, 0.35, 0.00]
    ],
    [
        [0.00, 0.52, 0.00],[0.25, 0.52, 0.00],[0.50, 0.52, 0.00],[0.75, 0.52, 0.00],[1.00, 0.52, 0.00],[1.25, 0.52, 0.00],[1.50, 0.52, 0.00],[1.75, 0.52, 0.00],[2.00, 0.52, 0.00],[2.25, 0.52, 0.00],[2.50, 0.52, 0.00],[2.75, 0.52, 0.00],[3.00, 0.52, 0.00],[3.25, 0.52, 0.00],[3.50, 0.52, 0.00],[3.75, 0.52, 0.00],[4.00, 0.52, 0.00],[4.25, 0.52, 0.00],[4.50, 0.52, 0.00],[4.75, 0.52, 0.00],[5.00, 0.52, 0.00]
    ],
    [
        [0.00, 0.69, 0.00],[0.25, 0.69, 0.00],[0.50, 0.69, 0.00],[0.75, 0.69, 0.00],[1.00, 0.69, 0.00],[1.25, 0.69, 0.00],[1.50, 0.69, 0.00],[1.75, 0.69, 0.00],[2.00, 0.69, 0.00],[2.25, 0.69, 0.00],[2.50, 0.69, 0.00],[2.75, 0.69, 0.00],[3.00, 0.69, 0.00],[3.25, 0.69, 0.00],[3.50, 0.69, 0.00],[3.75, 0.69, 0.00],[4.00, 0.69, 0.00],[4.25, 0.69, 0.00],[4.50, 0.69, 0.00],[4.75, 0.69, 0.00],[5.00, 0.69, 0.00]
    ],
    [
        [0.00, 0.87, 0.00],[0.25, 0.87, 0.00],[0.50, 0.87, 0.00],[0.75, 0.87, 0.00],[1.00, 0.87, 0.00],[1.25, 0.87, 0.00],[1.50, 0.87, 0.00],[1.75, 0.87, 0.00],[2.00, 0.87, 0.00],[2.25, 0.87, 0.00],[2.50, 0.87, 0.00],[2.75, 0.87, 0.00],[3.00, 0.87, 0.00],[3.25, 0.87, 0.00],[3.50, 0.87, 0.00],[3.75, 0.87, 0.00],[4.00, 0.87, 0.00],[4.25, 0.87, 0.00],[4.50, 0.87, 0.00],[4.75, 0.87, 0.00],[5.00, 0.87, 0.00]
    ],
    [
        [0.00, 1.04, 0.00],[0.25, 1.04, 0.00],[0.50, 1.04, 0.00],[0.75, 1.04, 0.00],[1.00, 1.04, 0.00],[1.25, 1.04, 0.00],[1.50, 1.04, 0.00],[1.75, 1.04, 0.00],[2.00, 1.04, 0.00],[2.25, 1.04, 0.00],[2.50, 1.04, 0.00],[2.75, 1.04, 0.00],[3.00, 1.04, 0.00],[3.25, 1.04, 0.00],[3.50, 1.04, 0.00],[3.75, 1.04, 0.00],[4.00, 1.04, 0.00],[4.25, 1.04, 0.00],[4.50, 1.04, 0.00],[4.75, 1.04, 0.00],[5.00, 1.04, 0.00]
    ],
    [
        [0.00, 1.22, 0.00],[0.25, 1.22, 0.00],[0.50, 1.22, 0.00],[0.75, 1.22, 0.00],[1.00, 1.22, 0.00],[1.25, 1.22, 0.00],[1.50, 1.22, 0.00],[1.75, 1.22, 0.00],[2.00, 1.22, 0.00],[2.25, 1.22, 0.00],[2.50, 1.22, 0.00],[2.75, 1.22, 0.00],[3.00, 1.22, 0.00],[3.25, 1.22, 0.00],[3.50, 1.22, 0.00],[3.75, 1.22, 0.00],[4.00, 1.22, 0.00],[4.25, 1.22, 0.00],[4.50, 1.22, 0.00],[4.75, 1.22, 0.00],[5.00, 1.22, 0.00]
    ],
    [
        [0.00, 1.39, 0.00],[0.25, 1.39, 0.00],[0.50, 1.39, 0.00],[0.75, 1.39, 0.00],[1.00, 1.39, 0.00],[1.25, 1.39, 0.00],[1.50, 1.39, 0.00],[1.75, 1.39, 0.00],[2.00, 1.39, 0.00],[2.25, 1.39, 0.00],[2.50, 1.39, 0.00],[2.75, 1.39, 0.00],[3.00, 1.39, 0.00],[3.25, 1.39, 0.00],[3.50, 1.39, 0.00],[3.75, 1.39, 0.00],[4.00, 1.39, 0.00],[4.25, 1.39, 0.00],[4.50, 1.39, 0.00],[4.75, 1.39, 0.00],[5.00, 1.39, 0.00]
    ],
    [
        [0.00, 1.56, 0.00],[0.25, 1.56, 0.00],[0.50, 1.56, 0.00],[0.75, 1.56, 0.00],[1.00, 1.56, 0.00],[1.25, 1.56, 0.00],[1.50, 1.56, 0.00],[1.75, 1.56, 0.00],[2.00, 1.56, 0.00],[2.25, 1.56, 0.00],[2.50, 1.56, 0.00],[2.75, 1.56, 0.00],[3.00, 1.56, 0.00],[3.25, 1.56, 0.00],[3.50, 1.56, 0.00],[3.75, 1.56, 0.00],[4.00, 1.56, 0.00],[4.25, 1.56, 0.00],[4.50, 1.56, 0.00],[4.75, 1.56, 0.00],[5.00, 1.56, 0.00]
    ],
    [
        [0.00, 1.74, 0.00],[0.25, 1.74, 0.00],[0.50, 1.74, 0.00],[0.75, 1.74, 0.00],[1.00, 1.74, 0.00],[1.25, 1.74, 0.00],[1.49, 1.74, 0.00],[1.74, 1.74, 0.00],[1.99, 1.74, 0.00],[2.24, 1.74, 0.00],[2.49, 1.74, 0.00],[2.74, 1.74, 0.00],[2.99, 1.74, 0.00],[3.24, 1.74, 0.00],[3.49, 1.74, 0.00],[3.74, 1.74, 0.00],[3.99, 1.74, 0.00],[4.24, 1.74, 0.00],[4.48, 1.74, 0.00],[4.73, 1.74, 0.00],[4.98, 1.74, 0.00]
    ],
    [
        [0.00, 1.91, 0.00],[0.25, 1.91, 0.00],[0.50, 1.91, 0.00],[0.74, 1.91, 0.00],[0.99, 1.91, 0.00],[1.24, 1.91, 0.00],[1.49, 1.91, 0.00],[1.73, 1.91, 0.00],[1.98, 1.91, 0.00],[2.23, 1.91, 0.00],[2.48, 1.91, 0.00],[2.72, 1.91, 0.00],[2.97, 1.91, 0.00],[3.22, 1.91, 0.00],[3.47, 1.91, 0.00],[3.71, 1.91, 0.00],[3.96, 1.91, 0.00],[4.21, 1.91, 0.00],[4.46, 1.91, 0.00],[4.70, 1.91, 0.00],[4.95, 1.91, 0.00]
    ],
    [
        [0.00, 2.08, 0.00],[0.25, 2.08, 0.00],[0.49, 2.08, 0.00],[0.74, 2.08, 0.00],[0.98, 2.08, 0.00],[1.23, 2.08, 0.00],[1.47, 2.08, 0.00],[1.72, 2.08, 0.00],[1.96, 2.08, 0.00],[2.21, 2.08, 0.00],[2.45, 2.08, 0.00],[2.70, 2.08, 0.00],[2.94, 2.08, 0.00],[3.19, 2.08, 0.00],[3.43, 2.08, 0.00],[3.68, 2.08, 0.00],[3.92, 2.08, 0.00],[4.17, 2.08, 0.00],[4.41, 2.08, 0.00],[4.66, 2.08, 0.00],[4.90, 2.08, 0.00]
    ],
    [
        [0.00, 2.26, 0.00],[0.24, 2.26, 0.00],[0.48, 2.26, 0.00],[0.73, 2.26, 0.00],[0.97, 2.26, 0.00],[1.21, 2.26, 0.00],[1.45, 2.26, 0.00],[1.69, 2.26, 0.00],[1.94, 2.26, 0.00],[2.18, 2.26, 0.00],[2.42, 2.26, 0.00],[2.66, 2.26, 0.00],[2.90, 2.26, 0.00],[3.15, 2.26, 0.00],[3.39, 2.26, 0.00],[3.63, 2.26, 0.00],[3.87, 2.26, 0.00],[4.11, 2.26, 0.00],[4.36, 2.26, 0.00],[4.60, 2.26, 0.00],[4.84, 2.26, 0.00]
    ],
    [
        [0.00, 2.43, 0.00],[0.24, 2.43, 0.00],[0.48, 2.43, 0.00],[0.71, 2.43, 0.00],[0.95, 2.43, 0.00],[1.19, 2.43, 0.00],[1.43, 2.43, 0.00],[1.66, 2.43, 0.00],[1.90, 2.43, 0.00],[2.14, 2.43, 0.00],[2.38, 2.43, 0.00],[2.62, 2.43, 0.00],[2.85, 2.43, 0.00],[3.09, 2.43, 0.00],[3.33, 2.43, 0.00],[3.57, 2.43, 0.00],[3.80, 2.43, 0.00],[4.04, 2.43, 0.00],[4.28, 2.43, 0.00],[4.52, 2.43, 0.00],[4.76, 2.43, 0.00]
    ],
    [
        [0.00, 2.60, 0.00],[0.23, 2.60, 0.00],[0.46, 2.60, 0.00],[0.70, 2.60, 0.00],[0.93, 2.60, 0.00],[1.16, 2.60, 0.00],[1.39, 2.60, 0.00],[1.63, 2.60, 0.00],[1.86, 2.60, 0.00],[2.09, 2.60, 0.00],[2.32, 2.60, 0.00],[2.56, 2.60, 0.00],[2.79, 2.60, 0.00],[3.02, 2.60, 0.00],[3.25, 2.60, 0.00],[3.49, 2.60, 0.00],[3.72, 2.60, 0.00],[3.95, 2.60, 0.00],[4.18, 2.60, 0.00],[4.42, 2.60, 0.00],[4.65, 2.60, 0.00]
    ],
    [
        [0.00, 2.78, 0.00],[0.23, 2.78, 0.00],[0.45, 2.78, 0.00],[0.68, 2.78, 0.00],[0.90, 2.78, 0.00],[1.13, 2.78, 0.00],[1.35, 2.78, 0.00],[1.58, 2.78, 0.00],[1.81, 2.78, 0.00],[2.03, 2.78, 0.00],[2.26, 2.78, 0.00],[2.48, 2.78, 0.00],[2.71, 2.78, 0.00],[2.93, 2.78, 0.00],[3.16, 2.78, 0.00],[3.39, 2.78, 0.00],[3.61, 2.78, 0.00],[3.84, 2.78, 0.00],[4.06, 2.78, 0.00],[4.29, 2.78, 0.00],[4.52, 2.78, 0.00]
    ],
    [
        [0.00, 2.95, 0.00],[0.22, 2.95, 0.00],[0.43, 2.95, 0.00],[0.65, 2.95, 0.00],[0.87, 2.95, 0.00],[1.09, 2.95, 0.00],[1.30, 2.95, 0.00],[1.52, 2.95, 0.00],[1.74, 2.95, 0.00],[1.96, 2.95, 0.00],[2.17, 2.95, 0.00],[2.39, 2.95, 0.00],[2.61, 2.95, 0.00],[2.83, 2.95, 0.00],[3.04, 2.95, 0.00],[3.26, 2.95, 0.00],[3.48, 2.95, 0.00],[3.69, 2.95, 0.00],[3.91, 2.95, 0.00],[4.13, 2.95, 0.00],[4.35, 2.95, 0.00]
    ],
    [
        [0.00, 3.13, 0.00],[0.21, 3.13, 0.00],[0.41, 3.13, 0.00],[0.62, 3.13, 0.00],[0.83, 3.13, 0.00],[1.03, 3.13, 0.00],[1.24, 3.13, 0.00],[1.44, 3.13, 0.00],[1.65, 3.13, 0.00],[1.86, 3.13, 0.00],[2.06, 3.13, 0.00],[2.27, 3.13, 0.00],[2.48, 3.13, 0.00],[2.68, 3.13, 0.00],[2.89, 3.13, 0.00],[3.09, 3.13, 0.00],[3.30, 3.13, 0.00],[3.51, 3.13, 0.00],[3.71, 3.13, 0.00],[3.92, 3.13, 0.00],[4.13, 3.13, 0.00]
    ],
    [
        [0.00, 3.30, 0.00],[0.19, 3.30, 0.00],[0.38, 3.30, 0.00],[0.57, 3.30, 0.00],[0.76, 3.30, 0.00],[0.95, 3.30, 0.00],[1.14, 3.30, 0.00],[1.34, 3.30, 0.00],[1.53, 3.30, 0.00],[1.72, 3.30, 0.00],[1.91, 3.30, 0.00],[2.10, 3.30, 0.00],[2.29, 3.30, 0.00],[2.48, 3.30, 0.00],[2.67, 3.30, 0.00],[2.86, 3.30, 0.00],[3.05, 3.30, 0.00],[3.24, 3.30, 0.00],[3.43, 3.30, 0.00],[3.62, 3.30, 0.00],[3.82, 3.30, 0.00]
    ],
    [
        [0.00, 3.47, 0.00],[0.15, 3.47, 0.00],[0.30, 3.47, 0.00],[0.45, 3.47, 0.00],[0.60, 3.47, 0.00],[0.75, 3.47, 0.00],[0.90, 3.47, 0.00],[1.05, 3.47, 0.00],[1.20, 3.47, 0.00],[1.35, 3.47, 0.00],[1.50, 3.47, 0.00],[1.65, 3.47, 0.00],[1.80, 3.47, 0.00],[1.95, 3.47, 0.00],[2.10, 3.47, 0.00],[2.25, 3.47, 0.00],[2.40, 3.47, 0.00],[2.55, 3.47, 0.00],[2.70, 3.47, 0.00],[2.85, 3.47, 0.00],[3.00, 3.47, 0.00]
    ]
];
