rblack42/math-magik-lpp/scad/math-magik-lpp/materials.scad

//###########################################
// materials.scad
// (c) 2021 - Roie R. Black
//*******************************************

tube_thickness = 1/64;
tube_height = 1/8;
post_diameter = 1/16;
