rblack42/math-magik-lpp/scad/math-magik-lpp/math_magik_lpp.scad

//####################################
// math-magik-lpp.scad
// (c) 2021 - Roie R. Black
//************************************
include <math_magik_lpp_pos.scad>
use <MMlib/position.scad>


use <prop/prop.scad>
use <fuselage/fuselage.scad>
use <wing/wing.scad>
use <stab/stab.scad>


module spinning_prop(ang=$t*360) {
  align(prop_pos)
    rotate([-ang,0,0])
      prop();
}

module math_magik_lpp() {
  align(fuse_pos) fuselage();
  align(wing_pos) wing();
  align(stab_pos) stab();
  spinning_prop();
}

//-------------------------------------
// debug display

math_magik_lpp();
