rblack42/math-magik-lpp/scad/fuselage/stab_post/stab_post_data.scad

//#####################################
// stab_post_data.scad
// (c) 2021 by Roie R. Black
//*************************************
include <../fuselage_data.scad>
include <../materials.scad>
include <colors.scad>


stab_post_color = WOOD_Balsa;
stab_post_height = 0.5 + tube_height;
