rblack42/math-magik-lpp/scad/fuselage/thrust_bearing/thrust_bearing_data.scad

//#####################################
// thrust_bearing_data.scad
// (c) 2021 by Roie R. Black
//=====================================
include <colors.scad>
include <../../math_magik_lpp_data.scad>
thb_thickness = 1/32;
thb_length = 1/2;
thb_height = -prop_z_offset;
thb_width = 1/16;
thb_front_height = thb_height/3;
thb_top_length = 3/16;
thb_wire_size = 0.025;


thrust_bearing_color = METAL_Aluminium;
density = 168.77;
