rblack42/math-magik-lpp/scad/fuselage/wing_post/wing_post_data.scad

//#####################################
// wing_post_data.scad
// (c) 2021 by Roie R. Black
//*************************************
include <../fuselage_data.scad>
include <colors.scad>
include <../../materials.scad>

wing_post_color = WOOD_Balsa;
wing_post_height = wing_elevation + tube_height;
