rblack42/math-magik-lpp/scad/math-magik-lpp/stab/stab_pos.scad

//########################################
// stab_pos.scad
// (c) 2021 - Roie R. Black
//****************************************
include <./stab_data.scad>
include <../materials.scad>
center_pos = [0,0,0,0,0,0];
left_tip_pos = [0, -center_span/2, 0, 0,0,0];
right_tip_pos = [0, center_span/2, 0, 0,0,0];
stab_le_mount_pos = [-post_diameter/2-tube_thickness,0,0,0,0,0];
stab_te_mount_pos = [max_stab_chord+post_diameter/2+tube_thickness,0,0,0,0,0];
