rblack42/math-magik-lpp/scad/math-magik-lpp/wing/wing.scad

//###################################################
// wing.scad
// (c) 2021 - Roie R. Black
//***************************************************
include <./wing_data.scad>
include <./wing_pos.scad>

use <MMlib/position.scad>

use <./center/center.scad>
use <./right_tip/right_tip.scad>
use <./left_tip/left_tip.scad>
use <./wing_mount/wing_mount.scad>


module wing() {
    align(right_tip_pos) right_tip();
    align(center_pos) center();
    align(left_tip_pos) left_tip();
    align(wing_le_mount_pos) wing_mount();
    align(wing_te_mount_pos) wing_mount();
}

wing();
