rblack42/math-magik-lpp/scad/wing/wing_mount/wing_mount.scad

//#################################################
// paper_tube.scad
// (c) 2021 Roie R. Black
//=================================================
include <../../materials.scad>
use <MMlib/paper_tube.scad>

module wing_mount() {
  color("Yellow")
	  paper_tube(post_diameter,tube_height,tube_thickness);
}

wing_mount();
