rblack42/math-magik-lpp/scad/fuselage/fin/covering/fin_covering.scad

use <function_grapher.scad>;
include <cover_points.scad>
include <colors.scad>

thickness = 0.001;
style = "FACES";  // LINES to show surface grid

module fin_covering() {
  color(GLASS_Blue)
  function_grapher(g_pts, thickness, style);
}

fin_covering();
