rblack42/math-magik-lpp/scad/fuselage/fin/rib1/fin_rib1.scad

//########################################
// fin_rib1.scad
// (c) 2021 - Roie R. Black
//****************************************
include <../fin_data.scad>

use <MMlib/square_spar.scad>

module fin_rib1() {
  square_spar(fin_chord, spar_size);
}

fin_rib1();
