rblack42/math-magik-lpp/scad/math-magik-lpp/prop/blade/blade_data.scad

//#######################################
// blade.scad prop_blade
// (c) 2021 - Roie R. Black
//***************************************

density = 5;
