rblack42/math-magik-lpp/scad/math-magik-lpp/prop/spar/spar.scad

//########################################
// spar.scad
// (c) 2021 - Roie R. Black
//****************************************
include <../prop_data.scad>
$fn = 64;


module spar() {
  color(prop_spar_color)
    union() {
      cylinder(
        r1=prop_spar_inner_radius,
        r2=prop_spar_outer_radius,
        h=prop_spar_length/2);
      rotate([0,180,0])
        cylinder(
          r1=prop_spar_inner_radius,
          r2=prop_spar_outer_radius,
          h=prop_spar_length/2);
    }
}

spar();
