rblack42/math-magik-lpp/scad/math-magik-lpp/prop/spar/spar_data.scad

//########################################
// spar_data.scad
// (c) 2021 - Roie R. Black
//****************************************

density = 5;
