rblack42/math-magik-lpp/scad/math-magik-lpp/prop/wire_shaft/wire_shaft_data.scad

//#####################################
// wire-shaft-data.scad
// (c) 2021 by Roie R. Black
//=====================================
include <colors.scad>

wire_diameter = 0.02;
hook_radius = 0.040;
length = 0.650;
stub_length = 0.050;


density = 490.792;
wire_color = METAL_Steel;
