rblack42/math-magik-lpp/scad/math-magik-lpp/stab/stab_mount/stab_mount_data.scad

//########################################
// stab_mount_data.scad
// (c) 2021 - Roie R. Black
//****************************************

density = 5;
