rblack42/math-magik-lpp/scad/math-magik-lpp/wing/center/center_pos.scad

//########################################
// center_pos.scad
// (c) 2021 - Roie R. Black
//****************************************
include <../wing_data.scad>

le_pos = [0,0,0,0,0,0];
te_pos = [max_wing_chord - spar_size,0,0,0,0,0];
rib1_pos = [spar_size,-center_span/2+spar_size/2,0,0,0,0];
rib2_pos = [spar_size,-center_span/4,0,0,0,0];
rib3_pos = [spar_size,0,0,0,0,0];
rib4_pos = [spar_size,center_span/4,0,0,0,0];
rib5_pos = [spar_size,center_span/2-spar_size/2,0,0,0,0];
covering_pos = [0,-center_span/2,spar_size,0,0,0];
