rblack42/math-magik-lpp/scad/math-magik-lpp/wing/right_tip/right_tip_data.scad

//########################################
// right_tip_data.scad
// (c) 2021 - Roie R. Black
//****************************************

density = 4;
mirror = "z";
