rblack42/math-magik-lpp/scad/math-magik-lpp/wing/wing_mount/wing_mount_data.scad

//########################################
// leading_edge_data.scad
// (c) 2021 - Roie R. Black
//****************************************

density = 5;
