rblack42/math-magik-lpp/scad/math-magik-lpp/fuselage/fin/arc/arc_data.scad

//########################################
// fin_arc_data.scad
// (c) 2021 - Roie R. Black
//****************************************

density = 4;
