rblack42/math-magik-lpp/notebooks/tikzfigures/test1.jpg

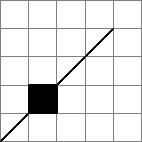
notebooks/tikzfigures/test1.jpg
